keefo/optic/worklogs/2026-09-21-focus-tools.md

# Dated Worklog: 2026-09-21 - Focus Tools: Histogram, Focus Peaking, Loupe

Status: **user-accepted** (2026-09-21): implemented, tested, deployed to the
Pi via `--assets`, and accepted by the user in the browser. Orca worktree
`focus-tools` (branch `focus-tools`, base `main` `0f06366`).

## Objective

Setup-visit tools on the dashboard's live preview, for the manual-focus
6 mm lens: a live **histogram** with clipping readouts, **focus peaking**
(edge highlight overlay), and a **loupe** (magnified crop around a chosen
point) with a numeric **sharpness score** you can maximise by turning the
focus ring. Picked by the user from the 2026-09-21 pro-features brainstorm.

## Design

**Everything runs in the browser, on frames the page already decodes.**
`app.js` parses the MJPEG multipart stream itself and decodes each frame
into `#preview` (`renderMjpegFrame`, after `await preview.decode()`). The
frame is a same-origin blob URL, so drawing it to a canvas does not taint
the canvas. So:

- There are no Rust, camera, or API changes and no daemon restart. The tools
  ship through the `--assets` deploy path.
- The processing cost lands on the viewing computer, not the Pi.
- It works in every browser. The page never relies on `<img>` rendering
  MJPEG natively.

The components:

- **New `src/web/focus-tools.js`.** It has two halves:
  - Pure functions that take `{data, width, height}` pixel data:
    - `computeHistogram` returns R/G/B/luma bins (Rec. 709 luma) and the
      shadow and highlight clipping fractions.
    - `toGray` and `sobelMagnitude`.
    - `peakingThreshold` returns the magnitude at a sensitivity
      percentile.
    - `sharpnessScore` returns the mean squared Sobel magnitude
      (Tenengrad).
    - `loupeRect` clamps the crop to the frame.
    - `clientToImagePoint` maps a click to image pixels under
      `object-fit: contain` letterboxing.

    They are exported for Node tests via `module.exports` when it exists.
  - A small UI controller on `window.OpticFocus`. `app.js` calls
    `OpticFocus.onFrame(img)` after each rendered frame, and
    `OpticFocus.clear()` when the preview is stopped or hidden.
- **Processing budget.** A frame is processed only if the previous one has
  finished; if not, the frame is skipped. The histogram and peaking run on
  a copy downscaled to at most a 960 px long edge. The loupe reads only its
  own crop (240 × 240 source pixels) from the full-resolution frame.
- **UI** (`index.html` and `styles.css`), under the preview:
  - Three toggle buttons (`aria-pressed`): Histogram, Peaking and Loupe.
  - A peaking sensitivity slider, shown only while peaking is on.
  - The **peaking overlay** is a `<canvas>` stacked on `#preview` with the
    same `object-fit: contain` and `pointer-events: none`.
  - The **histogram** is a small translucent canvas in the preview corner,
    plus shadow and highlight clipping percentages.
  - The **loupe** is a panel with the magnified crop. It shows the sharpness
    score, the best score so far (with a reset), and the source scale. That
    scale is "1:1 sensor pixels" only when the frame is 4056 px wide
    (Master Archive with downsample off); otherwise it reads "preview
    pixels". Clicking the preview moves the focus point; the default is the
    centre.
  - The toggle state is remembered per viewer in `localStorage`, wrapped
    in try/catch. The page works without it.
- `biome.json`: add `src/web/focus-tools.js`.
- CI: the web-lint job also runs `node --test tests/web`.

**Out of scope** (possible follow-ups):

- A true sensor-resolution crop at every profile, through libcamera
  `ScalerCrop` on the Pi (a Rust and camera change).
- Clipping zebras on the image.
- Waveform or RGB parade views.

## Acceptance Criteria

1. The histogram updates with the live preview, and its clipping
   percentages respond to over- and under-exposure.
2. Peaking highlights in-focus edges. The highlighted area grows as focus
   improves, and the sensitivity slider changes how much is highlighted.
3. The loupe shows a magnified crop at the clicked point, labelled with the
   right scale, and its sharpness score peaks at best focus.
4. All three tools are off by default and cost nothing when off. There is
   no visible slowdown of the preview on a typical laptop, including the
   Master Archive full-resolution 2 fps preview.
5. Stopping or freezing the preview (capture) doesn't break the tools. The
   overlays hide or keep the last frame, and they resume with the stream.
6. Existing behaviour is unchanged: capture, profile switching, downsample,
   the responsiveness measurement, and Biome and `cargo test`.

## Test Plan (before implementation)

Local (macOS):

1. `node --test tests/web` covers the pure functions:
   - Histogram: all-black gives 100% shadow clip; all-white gives 100%
     highlight clip; a 2-value image puts counts in the right bins; luma
     weights are right for pure red, green and blue.
   - Sobel and peaking: a vertical step edge gives magnitude only at the
     edge columns, and the threshold at a high percentile keeps only edge
     pixels.
   - Sharpness: a sharp step scores higher than the same step box-blurred.
   - `loupeRect` clamps at all four corners, and handles crops larger than
     the frame.
   - `clientToImagePoint` is right for letterboxing on both axes, and for a
     click outside the image.
2. `node --check` on the JS files; Biome 2.5.14 `ci` (via `npx`).
3. `cargo test` (the `web.rs` asset tests, plus a new assertion that
   `index.html` loads `focus-tools.js`).
4. CI on the PR.

On the Pi (needs user approval for an `--assets` deploy; no daemon restart):

5. The served `/focus-tools.js` matches the branch.
6. User browser acceptance of criteria 1–5, in Master Archive (full and
   downsampled) and in one small-preview profile.

## Handover (2026-09-21): work done so far, uncommitted in this worktree

Done:

- `src/web/focus-tools.js` (new): the pure functions and the browser
  controller (`window.OpticFocus.onFrame` / `.clear`), as designed above.
  Two design refinements from the draft:
  - Peaking uses an **absolute** Sobel threshold (`peakingThreshold`:
    220 → 40), not a percentile. A defocused frame must light up less.
  - The loupe scores a 160 px source crop at 1:1 and shows it at 2×,
    nearest-neighbour.
- `tests/web/focus-tools.test.js` (new): `node --test tests/web`.
  **12/12 pass** (Node 26.8.2, macOS).
- `src/web/index.html`:
  - loads `/focus-tools.js` before `/app.js`;
  - adds the peaking overlay canvas and histogram panel inside
    `.preview-frame`;
  - adds the focus-tools toolbar (3 toggles + sensitivity slider) and the
    loupe panel above the downsample option.
- `src/web/app.js`: two hooks. `window.OpticFocus?.onFrame(elements.preview)`
  runs after `recordRenderedFrame`, so the latency measurement is
  unaffected; `window.OpticFocus?.clear()` runs in `hidePreview`.
- `src/web/styles.css`: the focus-tools block is appended at the end.
- `biome.json`: `src/web/focus-tools.js` added to `files.includes`.
- `src/web.rs`: new test `focus_tools_are_wired_into_the_dashboard`. It
  checks the script order and the hooks, and that every `$("#id")` in
  focus-tools.js exists in index.html. `cargo test --locked`: **171
  passed** (macOS).
- `node --check src/web/focus-tools.js`: ok.

Remaining:

1. Biome 2.5.14 `ci` locally (not installed; try
   `npx @biomejs/biome@2.5.14 ci`), and fix anything it reports.
2. CI: add `node --test tests/web` to the `web-lint` job in
   `.github/workflows/ci.yml`. Check `scripts/ci-changed-scope.sh`: a
   `tests/web` change must not count as docs-only.
3. Write `docs/optic-daemon-focus-tools.md` (referenced from
   focus-tools.js). Add a short pointer in `docs/optic-daemon.md` (the
   dashboard section) and the README Camera Daemon paragraph.
4. With user approval: `./scripts/build-deploy-optic-daemon.sh --assets`
   (no daemon restart). Check that the served `/focus-tools.js` matches
   the branch. Then the user does the browser acceptance of criteria 1–5
   in Master Archive (full and downsampled) and one small-preview profile.
5. Close this worklog, then commit, push the branch and open a PR (with
   user approval).

## Progress (2026-09-21, Orca agent session): Remaining items 1–3

1. **Biome 2.5.14 `ci`** (`npx @biomejs/biome@2.5.14 ci`). The first run
   found 2 errors and 1 warning, all fixed:
   - warning `lint/suspicious/noRedundantUseStrict` in `focus-tools.js`:
     removed `"use strict";` (no other dashboard script uses it; the file is
     a classic script and does not depend on strict mode);
   - `format` in `focus-tools.js` (`clear()`): applied `biome format --write`;
   - `lint/a11y/useSemanticElements` on `<div role="group">` in
     `index.html`: it is now a `<fieldset class="focus-tools"
     aria-label="Focus tools">`. `.focus-tools` in `styles.css` now sets
     `flex-direction: row`, `min-width: 0` and `margin`, so the global
     `fieldset` rules (including the narrow-screen `flex-direction:
     column`) do not stack the toggles.

   Re-run: `Checked 11 files ... No fixes applied.`, exit 0.
2. **CI:** `web-lint` in `.github/workflows/ci.yml` now also runs
   `node --version && node --test tests/web` on the runner's preinstalled
   Node. No new action or npm dependency; the tests use `node:test` only.
   `scripts/ci-changed-scope.sh` needed no change, since only `*.md`,
   `docs/*`, `worklogs/*` and `case/*` count as docs. Checked:
   `printf 'tests/web/focus-tools.test.js\nworklogs/x.md\n' |
   scripts/ci-changed-scope.sh` gives `docs_only=false`. Documented in
   `docs/optic-daemon-ci-cd.md` §4 and §5.1.
3. **Docs:** new `docs/optic-daemon-focus-tools.md`. Pointers added in
   `docs/optic-daemon.md` (Web Service, Responsibilities) and in the README
   Camera Daemon paragraph.

Local re-verification after these changes (macOS, Node 26.8.2):

- `node --check src/web/focus-tools.js`: ok. `node --test tests/web`:
  12/12 pass.
- `npx @biomejs/biome@2.5.14 ci`: clean.
- `cargo fmt --check`: it flagged the new `src/web.rs` test (one long
  `assert!`). Fixed with `cargo fmt`, which changed only `src/web.rs`.
- `cargo test --locked`: 171 passed, including
  `focus_tools_are_wired_into_the_dashboard`.
- `cargo clippy --locked --all-targets -- -D warnings`: clean.

Pre-deploy check of the Pi (read-only):

- `optic-daemon.service` is active.
- `/focus-tools.js` returns 500 (the missing-asset response).
- Every tracked `src/web` file the Pi serves matches `HEAD` (`0f06366`),
  and `origin/main` has not moved. So an `--assets` deploy from this
  worktree changes only `app.js`, `index.html` and `styles.css`, and adds
  `focus-tools.js`. It does not overwrite another track's files.

Doc mismatch noticed, not fixed here (outside this track): the README Camera
Daemon paragraph still says the daemon runs as "`liam`'s persistent systemd
user service", but since PR #12 it is a system service.

## Deploy (2026-09-21, user-approved): item 4

- `./scripts/build-deploy-optic-daemon.sh --assets`: the Pi-side Biome run
  checked 11 files with no fixes, it installed with rollback protection, and
  it ended with
  `SUCCESS: static web assets deployed and verified at http://optic.local:8000/`.
  The only ERROR in the service log (05:11:29 UTC,
  `failed to load web asset ... focus-tools.js`) was the pre-deploy
  read-only probe, from before the file existed.
- Served content vs the worktree (SHA-256 over HTTP): `focus-tools.js`,
  `app.js`, `index.html`, `styles.css`, `footer.js` and `scheduler.js` all
  **match**. `/focus-tools.js` returns 200 `text/javascript; charset=utf-8`.
- No restart: `optic-daemon.service` is active, with `ActiveEnterTimestamp`
  unchanged at 21:44:05 PDT (before the deploy).

Status: **deployed**. The browser acceptance of criteria 1–5 is pending
with the user.

## Change from user acceptance (2026-09-21): drag to move the loupe

User feedback during acceptance: clicking moves the loupe, but "I
naturally click down and drag, hope it would follow my drag, but it does
not." I reproduced this in Chrome: a click moved the box from the centre to
the top-left, and a drag did nothing beyond the initial press.

Plan:

- Replace the `click` handler on `#preview` with pointer events. While the
  loupe is on:
  - `pointerdown` (primary button) places the point and captures the
    pointer;
  - `pointermove` while captured follows the pointer, clamped to the image
    edges so dragging past the letterbox pins the box to the edge;
  - `pointerup` or `pointercancel` ends the drag.
- Redraws during a drag are coalesced to one per animation frame. Moving
  the point resets "best", as a click already did.
- Suppress the browser's native image drag (`dragstart`) and set
  `touch-action: none` while the loupe is on, so touch drags work.
- `clientToImagePoint` gains an optional `clamp` argument. The default
  (null outside the image) is unchanged for the initial press.

Tests first: in `node --test tests/web`, `clientToImagePoint` with
`clamp=true` pins points in the letterbox and outside the element to the
image edges, and leaves inside points unchanged. The existing tests must
still pass.

Acceptance: press on the preview and drag. The green box and the loupe
crop follow the pointer smoothly (Master Archive full, downsampled, and a
small profile). Dragging past the image edge pins the box to the edge, and
a plain click still works.

Implementation (drag):

- **`focus-tools.js`:**
  - `clientToImagePoint(..., clamp = false)`;
  - the `click` handler replaced by `pointerdown`, `pointermove`,
    `pointerup` and `pointercancel` with pointer capture;
  - rAF-coalesced redraws (`moveLoupeTo`);
  - `dragstart` suppressed while the loupe is on.
- **`styles.css`:** `img.loupe-target` gets `touch-action: none;
  user-select: none`.
- **`index.html`:** the hint now reads "Click or drag on the preview to move
  the loupe."
- **`docs/optic-daemon-focus-tools.md`:** §2 table and §3.4, §3.5 updated.

Verification:

- The new test failed first (12 pass, 1 fail) and passes after the change:
  `node --test tests/web` gives 13/13.
- `npx @biomejs/biome@2.5.14 ci`: clean. `cargo test --locked`: 171
  passed.
- The user approved a second `--assets` deploy:
  - Pi Biome clean; the script ended with `SUCCESS: static web assets
    deployed and verified`.
  - Served `focus-tools.js`, `index.html`, `styles.css` and `app.js` match
    the worktree (SHA-256).
  - `ActiveEnterTimestamp` unchanged at 21:44:05 PDT, so no restart.
- Agent browser check (Chrome, Master Archive, downsampled 1352 × 1014
  preview):
  - dragging from the centre moved the box and the crop to the top-left;
  - dragging far past the bottom-right corner pinned the box at that
    corner;
  - there were no console errors.
  - This is an agent check, not user acceptance.

## Close (2026-09-21)

**User acceptance:** after the drag change, the user checked the dashboard
and replied "looks good commit create pr". Criteria 1–5 are accepted.
Criterion 6 is covered by `cargo test` (171), Biome `ci` and the unchanged
latency hook order.

**Files changed:**

- New:
  - `src/web/focus-tools.js`
  - `tests/web/focus-tools.test.js`
  - `docs/optic-daemon-focus-tools.md`
  - this worklog
- Modified:
  - `src/web/app.js` (2 hooks)
  - `src/web/index.html`
  - `src/web/styles.css` (focus-tools block at the end)
  - `src/web.rs` (test `focus_tools_are_wired_into_the_dashboard`)
  - `biome.json`
  - `.github/workflows/ci.yml` (`node --test tests/web` in `web-lint`)
  - `docs/optic-daemon-ci-cd.md`
  - `docs/optic-daemon.md`
  - `README.md`
- Not changed: `Cargo.toml` (version stays 0.1.31), Rust runtime code,
  camera, API and systemd.

**Final results:**

- `node --test tests/web`: 13/13.
- `npx @biomejs/biome@2.5.14 ci`: clean.
- `cargo fmt --check`: clean. `cargo clippy --locked --all-targets -D
  warnings`: clean. `cargo test --locked`: 171 passed.
- Deployed assets match the branch, with no daemon restart.
- GitHub CI runs on the PR, including the new Node step.

**Limitations and follow-ups:**

- The loupe is 1:1 with the sensor only in Master Archive with downsampling
  off. A sensor-resolution crop in every profile would need libcamera
  `ScalerCrop` (Rust and camera).
- No zebras, waveform or RGB parade.
- The histogram comes from the JPEG preview, not RAW.
- The new CI step relies on the runner's preinstalled Node. If a future
  image drops Node, add a SHA-pinned `actions/setup-node`.
- README mismatch, outside this track: it still says "systemd user
  service" (it has been a system service since PR #12).

## CI fix (2026-09-21, after PR #13 opened)

PR #13 CI: `Biome (web assets)` failed on both the push and pull_request
runs. `biome ci` passed; the new step failed. The runner has Node
**v22.23.2**, which treats `node --test tests/web` as a module path:
`Error: Cannot find module '/home/runner/work/optic/optic/tests/web'`,
with 0 tests run. Local Node 26 discovers test files in a directory, which
is why it passed locally. The other checks passed: Rust (Debian 13
arm64), Timelapse tool (macOS) and Detect changed scope.

Fix: CI now runs `node --test tests/web/*.test.js` (bash expands the glob;
this works on every Node that has `node:test`). The same form is now used
in the test-file header comment, `docs/optic-daemon-ci-cd.md` (§4 and
§5.1) and `docs/optic-daemon-focus-tools.md`. The lesson is recorded in
`AGENTS.md`, under Environment and Tooling Constraints.

Local check: `node --test tests/web/*.test.js` gives 13/13.
