keefo/optic/worklogs/2026-09-20-ci-phase1-gates.md

# Dated Worklog: 2026-09-20 - CI Phase 1: GitHub Actions Gates

Status: **implemented and tested on GitHub Actions**. All acceptance
criteria (AC1–AC6) passed.

- Nothing was deployed. The Pi was not touched.
- The CI-built binary has **not** been hardware-validated; that is phase 2.
- Awaiting user acceptance.

Plan: [`docs/optic-daemon-ci-cd.md`](../docs/optic-daemon-ci-cd.md) §7 phase 1.
Research: [`2026-09-20-github-ci-cd-plan.md`](2026-09-20-github-ci-cd-plan.md).
User decisions (2026-09-20): implement phase 1; D2 = add `rust-toolchain.toml`.

## Objective

Run the deploy script's gates on every push and PR, on GitHub-hosted runners:

- fmt;
- test;
- strict Clippy;
- Biome;
- the release build, with `ldd` and version checks.

The release binary is kept as a downloadable CI artifact. There is no
release or deploy step in this phase.

## Scope

1. `rust-toolchain.toml` (`channel = "1.98.1"`, with rustfmt and Clippy).
   The deploy script reads `RUST_VERSION` from it instead of hard-coding it.
2. The Biome file list moves into `biome.json` `files.includes`. The deploy
   script and CI both run Biome without explicit paths.
3. `scripts/ci-install-build-deps.sh` installs the native packages in a
   `debian:trixie` container:
   - it adds the Raspberry Pi archive with the key fingerprint pinned to
     `CF8A1AF502A2AA2D763BAE7E82B129927FA3303E`;
   - it installs the exact `required_packages` list parsed from
     `scripts/build-deploy-optic-daemon.sh`, so the pins exist in one place.
4. `.github/workflows/ci.yml` with two jobs, `web-lint` and `rust-arm64`.
5. `.github/dependabot.yml` for `github-actions` only.

Out of scope: `release.yml`, the `--release` deploy mode, any Pi changes,
and branch protection (D1).

## Acceptance Criteria

- AC1: `actionlint` reports no errors on `ci.yml`, and `bash -n` passes on
  the changed scripts.
- AC2: Biome 2.5.14 with the new `files.includes` checks exactly the nine
  files the script checked before (`app.js`, `index.html`, `scheduler.js`,
  `scheduler.html`, `capture-history.js`, `capture-history.html`,
  `config.js`, `config.html`, `footer.js`). It passes on the current tree
  and fails on a deliberately mis-formatted file.
- AC3: The `required_packages` parse yields the same nine pins the script
  uses.
- AC4: Parsing `rust-toolchain.toml` yields `1.98.1`. Local cargo still
  passes fmt, test and Clippy.
- AC5: **(requires a push, gated on user approval)**
  - A GitHub Actions run on this branch is green in both jobs.
  - The Linux test count is recorded.
  - The `ldd` and version checks pass and the artifact is downloadable.
  - Cold and warm durations are recorded.
- AC6 (negative, requires a push): a deliberate fmt violation turns the run
  red. Run it once, then revert.

## Failure Cases to Watch

- The RPi repo may pull in newer packages than the pins, causing an apt
  resolution conflict. The script fails loudly; it does not float versions.
- Clippy may fail with LLVM 19 vs 22 in the container. If so, port the
  deploy script's wrapper and record that.
- bindgen may be unable to find headers or libclang. `LIBCLANG_PATH` and
  `BINDGEN_EXTRA_CLANG_ARGS` mirror the Pi script.
- Tests may assume a host-specific environment such as tmpfs or `/proc`.

## Target Environments

- Local macOS: static checks, Biome, and cargo on the non-Linux code path.
- GitHub-hosted `ubuntu-24.04-arm` with a `debian:trixie` container: the
  real CI (AC5 and AC6).
- The Pi is **not** touched. Deploy-script edits are checked with `bash -n`
  and local extraction tests only. A real deploy is needed to hardware-verify
  them.

## Implementation Summary

Files changed:

- `rust-toolchain.toml` (new): `channel = "1.98.1"`, with the rustfmt and
  Clippy components and the minimal profile.
- `biome.json`:
  - adds `files.includes` with the nine web files;
  - adds a trailing newline. The file had none before, and Biome now checks
    its own config once no paths are passed, so the missing newline was a
    new failure.
- `scripts/build-deploy-optic-daemon.sh`:
  - uploads `rust-toolchain.toml` and requires it to be present;
  - on the Pi, reads `RUST_VERSION` from it and validates the format;
  - runs `"$HOME/biome" check` with no paths;
  - adds a comment documenting that CI parses `required_packages`.
- `scripts/ci-install-build-deps.sh` (new): the root-only installer for the
  arm64 trixie container. It:
  - takes the Raspberry Pi archive key from the
    `raspberrypi-archive-keyring_2025.1+rpt1_all.deb` package, pinned by
    SHA-256, then checks the key fingerprint;
  - writes a deb822 source with `Signed-By`;
  - installs the parsed pins with `--print-packages` available for dry runs;
  - uses a read loop instead of `mapfile`, because macOS bash 3.2 has no
    `mapfile`.
- `.github/workflows/ci.yml` (new) has two jobs, `web-lint` and
  `rust-arm64`:
  - every action is pinned to a commit SHA: checkout v7.0.1
    `3d3c42e5…`, setup-biome v2.7.1 `4c91541e…`, rust-cache v2.9.2
    `6323deb1…`, upload-artifact v7.0.1 `043fb46d…`;
  - SHAs were resolved with `git ls-remote`, using the peeled `^{}` commit
    for annotated tags.
- `.github/dependabot.yml` (new): weekly grouped `github-actions` updates
  only.
- Docs: `docs/optic-daemon-ci-cd.md` (status, §2, §5.1, D2 resolved) and
  `docs/optic-daemon-build-environment.md` (the new single sources).

Design deviation from the plan: CI installs the **same** nine
`required_packages` pins as the Pi, with
`LIBCLANG_PATH=/usr/lib/aarch64-linux-gnu`, instead of the separately
listed `libclang-19-dev`. This keeps the Pi and CI on one pin list. The plan
doc was updated to match.

## Validation

Environment: the macOS development host. No Linux or arm64 container was
available locally: no Docker, and the `vmpi-builder` Lima VM is x86_64
without qemu-user.

| AC | Command | Observed |
| --- | --- | --- |
| AC1 | `actionlint` 1.7.12 with shellcheck 0.11.0 on `PATH` | First run: 2× SC2094 (info). The checksum step read and wrote `SHA256SUMS` in the same pipeline; fixed by writing to a temp file outside the hashed directory and then `mv`. Rerun: exit 0 |
| AC1 | `shellcheck scripts/ci-install-build-deps.sh` | SC1091 (info) on `. /etc/os-release`; added a `source=/dev/null` directive. Rerun: exit 0 |
| AC1 | `bash -n` on both scripts | OK. The deploy script's shellcheck finding count is unchanged vs `HEAD` (1 existing) |
| AC2 | Biome 2.5.14 (`npx @biomejs/biome@2.5.14`) `check --verbose` | The processed set is exactly the nine listed files, plus `biome.json` |
| AC2 | Baseline: `HEAD` `biome.json` with the old explicit nine paths | `Checked 9 files … No fixes applied` |
| AC2 | New `biome check` / `biome ci` before the newline fix | 1 error: `biome.json` format (missing trailing newline) |
| AC2 | New `biome check` / `biome ci` after the fix | `Checked 10 files`, exit 0 |
| AC2 | Negative test: a copy with a mis-formatted line appended to `footer.js` | `biome ci` exit 1, `biome check` exit 1 |
| AC3 | `scripts/ci-install-build-deps.sh --print-packages` | The nine pins, identical to `required_packages`. `--bogus` gives exit 1; running as non-root gives exit 1 "must run as root" |
| AC3 | Each pin is present in the Debian trixie and RPi trixie arm64 `Packages` indexes | 9/9 OK |
| AC4 | `sed` parse of `rust-toolchain.toml` | `1.98.1` |
| AC4 | Local `cargo fmt --check`, `cargo test --locked --all-targets`, `cargo clippy … -D warnings` (Homebrew cargo 1.98.1, which ignores `rust-toolchain.toml`) | fmt OK; `109 passed; 0 failed`; Clippy clean |
| AC5 | Run `35567448224` (commit `e04a755`) | **Failed** at "Install pinned native build dependencies". See Failures Encountered |
| AC5 | Run `35567649875` (commit `b09f7c4`, cold cache) | **Success.** Biome 5s; the Rust job took 4m35s in total |
| AC6 | Run `35568071487` (commit `64dabda`, a deliberate extra space in `src/main.rs` `fn main`) | **Failure** at the `cargo fmt` step (`Diff in …/src/main.rs:32`). Biome still passed. Reverted in `acc0002` |
| AC5 | Run `35568193008` (commit `acc0002`, warm cache) | **Success.** The Rust job took 1m45s in total |

AC5 details from run `35567649875`:

- Step times on a cold cache:
  - dependency install: 20s;
  - toolchain: 6s;
  - `cargo test`: 64s;
  - Clippy: 28s;
  - release build (LTO, `codegen-units = 1`): 100s;
  - cache save: 41s.
- Step times on a warm cache (run `35568193008`):
  - dependency install: 20s;
  - cache restore: 11s;
  - test: 9s;
  - Clippy: 3s;
  - release build: 39s.
- Linux tests: `112 passed; 0 failed` in the main target, plus
  `4 passed; 0 failed` in `libcamera_probe`. That is 116 in total, vs 109
  on macOS; the difference is the `cfg(target_os = "linux")` tests.
- Clippy `-D warnings` passed **without** the Pi's LLVM-isolating
  compiler wrapper, as expected, because the container installs libclang
  system-wide.
- `ldd` resolved every library with no `not found`. The binary links
  `/lib/aarch64-linux-gnu/libcamera.so.0.7`, `libcamera-base.so.0.7` and
  `libturbojpeg.so.0`. The embedded-version check for `0.1.29` passed.
- The artifact `optic-daemon-0.1.29-aarch64-linux-gnu-b09f7c437246` is
  about 2.0 MB and expires 2026-10-05. It was downloaded with
  `gh run download`, and `shasum -a 256 -c SHA256SUMS` reported 15/15 OK.
  `file` reports `ELF 64-bit LSB pie executable, ARM aarch64 … stripped`;
  it is 5,331,752 bytes, and the executable bit survived the round trip.
  `VERSION` is `0.1.29` and `COMMIT` is `b09f7c43…`.

The RPi archive key fingerprint was computed from
`raspberrypi.gpg.key` (sha256 `76603890…6d56`) with a Python OpenPGP v4
fingerprint calculation, because no `gpg` was available on the Mac or the
VM. Primary key: `CF8A1AF502A2AA2D763BAE7E82B129927FA3303E`, uid
"Raspberry Pi Archive Signing Key".

## Failures Encountered

- `mapfile: command not found` under the macOS bash 3.2. Replaced with a
  `while read` loop. `CLAUDE.md` asks for such findings to be recorded in
  `AGENTS.md`, but that file does not exist in this checkout (plan O4), so
  the finding is recorded here instead.
- Biome's config-file check exposed the missing trailing newline in
  `biome.json`. Fixed as described above.
- **First CI run failed:** apt refused the Raspberry Pi archive.
  - The error from `sqv` was `Signing key on CF8A1AF5…7FA3303E is not
    bound … SHA1 is not considered secure since 2026-02-01`. The key served
    at `raspberrypi.gpg.key` carries SHA-1 self-signatures (checked locally:
    the uid and subkey bindings are both SHA-1).
  - The `raspberrypi-archive-keyring 2025.1+rpt1` package ships the **same**
    key, with SHA-512 bindings, as `usr/share/keyrings/raspberrypi-archive-keyring.pgp`.
    The package's SHA-256 (`2e727149…60e4`) matched the RPi `Packages`
    index.
  - Fix (commit `b09f7c4`): download that `.deb`, check its pinned SHA-256
    and the key fingerprint, and use the `.pgp` as `Signed-By`.
  - The pinned fingerprint check itself had passed, which confirms it was
    matching the correct key.
- Command mistake: `git revert -q` does not exist (`git revert` has no
  quiet flag). Used `git revert --no-edit HEAD >/dev/null` instead. As
  with `mapfile`, this is recorded here because there is no `AGENTS.md`.

## Limitations and Next Steps

- Pinning `raspberrypi-archive-keyring` means CI fails loudly if the RPi
  archive rotates its key or withdraws that package version. That is the
  intended behaviour; update the pin deliberately.
- The branch history includes the AC6 negative-test commit and its revert
  (`64dabda`, `acc0002`), by design.
- The deploy-script edits (reading `RUST_VERSION` from the file, Biome with
  no paths) have **not** run on the Pi. The next real `build-deploy` run,
  full or `--assets`, will exercise them. Plan item O1: check that the Pi's
  `~/biome` is a 2.x version that supports `files.includes`.
- Nothing was deployed; phase 2 (a hardware test of the CI artifact) needs
  explicit approval.
