keefo/optic/worklogs/2026-09-20-scheduler-phase2e-capture-log-source-fix-and-doc-resolution.md

# Dated Worklog: 2026-09-20 - Scheduler Phase 2e: Capture-Log Source Fix, `triggered_by`, and Design-Doc Resolution

Status: **implemented, deployed, and verified.**

## Objective

Two small, explicitly-deferred follow-ups from the earlier
`2026-09-20-scheduler-capture-filename-tagging.md` worklog, plus closing
out the design doc's now-almost-entirely-resolved §14 open-decisions
list:

1. `optic_capture_log.rs::failure_capture_id` always said `testshot-`
   for a *failed* scheduler capture's synthetic log-only id, regardless
   of actual source.
2. `CaptureLogEntry.source` was a plain string with no structured record
   of which rule(s) triggered a scheduler capture.
3. `docs/optic-daemon-scheduler.md`'s top-of-file status and §14 still
   read as an in-progress design proposal despite Phase 1 and (as of
   tonight) most of Phase 2 being fully implemented and deployed.

## Implementation Summary

### `src/optic_capture_log.rs`

- Root cause of item 1: `CaptureLogEntry::new()` always hardcoded
  `source: "web_ui".to_owned()` internally and computed `capture_id`
  (via `derive_capture_id`/`failure_capture_id`) *before* the one caller
  that needed something different (`optic_scheduler.rs`'s `fire_capture`)
  patched `entry.source` afterward — too late for the id itself to ever
  reflect it.
- Fixed by threading the real `CaptureSource` (already known at both
  call sites — `web.rs`'s `capture()` has it on the incoming
  `CaptureRequest`, `optic_scheduler.rs`'s `fire_capture` constructs it
  directly) into `CaptureLogEntry::new()` as a new parameter, used by
  both `derive_capture_id`/`failure_capture_id` (for the id prefix) and
  to set `source`/the new `triggered_by` field correctly from the start
  — no more post-hoc patching.
- `CaptureLogEntry` gained `#[serde(default)] triggered_by: Vec<String>`
  — empty for `WebUi`, the firing rule slugs for `Scheduler`. No
  database schema migration needed: the whole entry is persisted
  verbatim as the `detail_json` column (per this module's own doc
  comment), so a new struct field just flows into that JSON blob.
  `#[serde(default)]` specifically so a `.log.json` file or database row
  written before this field existed still deserializes (as empty)
  rather than failing — matters because these files/rows are genuinely
  durable and outlive any given daemon version.
- `web.rs`/`optic_scheduler.rs` call sites: both now extract
  `request.source.clone()` *before* `request` is moved into
  `capture_to_stage`, and pass it through — `optic_scheduler.rs` no
  longer needs the post-hoc `entry.source = "scheduler".to_owned()`
  line at all, removed.

### `docs/optic-daemon-scheduler.md`

- Top-of-file `> Status:` line: "design proposal, not implemented" →
  reflects Phase 1 (shipped 2026-09-19) and Phase 2 (shipped
  2026-09-20), pointing at the dated worklogs for the actual record.
- §2's `Constraints` data-model prose: "`time_window` is the only field
  implemented today... the rest are Phase 2+" → all five fields are now
  implemented, dated accordingly.
- §14: added six new **Resolved** entries (merge-window duration bumped
  to 10s with the measured-data rationale; Station config as a plain
  manual dashboard form; the `astro` crate decision and why it
  eliminated the previously-separate lunar-crate research item;
  `Trigger::Ephemeris` fully implemented and live-verified; the Storage
  Forecaster; the dead-rule/overlap advisories) and updated the
  `testshot-`-prefix entry's "Not done" list to "now also done" for both
  previously-deferred items — turning §14 from a genuine open-questions
  list into what it now actually is, a resolved-decisions log with
  pointers to the worklog that implemented and verified each one.
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
