keefo/optic/src/optic_capture_log.rs

//! Passive observer of every capture request `optic_web` (and, later,
//! `optic_scheduler`) issues to `optic_camera`: durably records what was
//! requested, whether it succeeded, and basic output metadata, so capture
//! history survives past a single `tracing` session. See
//! `docs/optic-daemon-capture-log.md` for the full design and
//! `worklogs/2026-09-18-capture-history-module.md` for the decisions behind
//! this scope.
//!
//! Two best-effort writes per capture — neither can affect whether the
//! capture itself succeeded, and a failure in either is logged and
//! swallowed rather than surfaced to the HTTP caller:
//! - a `<capture_id>.log.json` file dropped into the capture directory,
//!   picked up and transferred by `optic_sync` exactly like the JPEG/DNG
//!   files it's paired with;
//! - a row in a local SQLite database, for fast Pi-side dashboard queries
//!   that per-file scanning can't answer efficiently (date-range counts,
//!   duration trends).

use std::{
    path::{Path, PathBuf},
    sync::{
        Arc, Mutex,
        atomic::{AtomicU64, Ordering},
    },
    time::{SystemTime, UNIX_EPOCH},
};

use rusqlite::{Connection, OptionalExtension};
use serde::{Deserialize, Serialize};
use tracing::warn;

use crate::camera::{
    CameraError, CameraSettings, CaptureFile, CaptureProfile, CaptureResult, CaptureSource,
};

static LAST_FAILURE_SUFFIX: AtomicU64 = AtomicU64::new(0);

/// One capture's worth of what was requested and what happened, persisted
/// verbatim as both the `.log.json` file body and the SQLite row's
/// `detail_json` column.
#[derive(Debug, Serialize, Deserialize)]
pub struct CaptureLogEntry {
    pub capture_id: String,
    pub source: String,
    /// The rule slug(s) that triggered this capture — empty for
    /// `CaptureSource::WebUi`, populated for `CaptureSource::Scheduler`.
    /// Structured alongside `source`'s plain string, per the design doc's
    /// own follow-up note (`docs/optic-daemon-scheduler.md` §3.1): lets
    /// the dashboard show/filter "what triggered this shot" without
    /// re-parsing filenames. `#[serde(default)]` so a `.log.json` file or
    /// database row written before this field existed still deserializes
    /// (as empty) rather than failing.
    #[serde(default)]
    pub triggered_by: Vec<String>,
    pub requested_at_unix_ms: u128,
    pub completed_at_unix_ms: u128,
    pub duration_ms: u128,
    pub profile: CaptureProfile,
    pub settings: CameraSettings,
    pub save_dng: bool,
    pub success: bool,
    pub error: Option<String>,
    pub files: Vec<CaptureFile>,
    pub bytes: u64,
    pub width: Option<u32>,
    pub height: Option<u32>,
    /// What the camera *actually* did: the output frame's own metadata
    /// (shutter, analogue gain, colour gains) and its brightness meter, as
    /// opposed to `settings`, which is what was **requested**. `None` for a
    /// failed capture or a backend that reports no metadata.
    /// `#[serde(default)]` so sidecars and rows written before this field
    /// existed still parse (`worklogs/2026-09-22-capture-exposure-metadata.md`).
    #[serde(default)]
    pub exposure: Option<crate::camera::CaptureExposure>,
}

impl CaptureLogEntry {
    /// Builds an entry from the same request fields and
    /// `Result<CaptureResult, CameraError>` the HTTP handler already has,
    /// without consuming it — `web.rs::capture()` still needs `outcome` to
    /// build its own response afterward.
    #[allow(clippy::too_many_arguments)]
    pub fn new(
        requested_at: SystemTime,
        completed_at: SystemTime,
        duration_ms: u128,
        profile: CaptureProfile,
        settings: CameraSettings,
        save_dng: bool,
        source: &CaptureSource,
        outcome: &Result<CaptureResult, CameraError>,
    ) -> Self {
        let capture_id = derive_capture_id(profile, source, outcome);
        let (source_str, triggered_by) = match source {
            CaptureSource::WebUi => ("web_ui".to_owned(), Vec::new()),
            CaptureSource::Scheduler { rule_slugs } => ("scheduler".to_owned(), rule_slugs.clone()),
        };
        let (success, error, files, bytes, width, height) = match outcome {
            Ok(result) => (
                true,
                None,
                result
                    .files
                    .iter()
                    .map(|file| CaptureFile {
                        filename: file.filename.clone(),
                        bytes: file.bytes,
                    })
                    .collect(),
                result.bytes,
                Some(result.width),
                Some(result.height),
            ),
            Err(error) => (false, Some(error.to_string()), Vec::new(), 0, None, None),
        };
        Self {
            capture_id,
            source: source_str,
            triggered_by,
            requested_at_unix_ms: unix_ms(requested_at),
            completed_at_unix_ms: unix_ms(completed_at),
            duration_ms,
            profile,
            settings,
            save_dng,
            success,
            error,
            files,
            bytes,
            width,
            height,
            exposure: outcome.as_ref().ok().and_then(|result| result.exposure),
        }
    }
}

fn unix_ms(time: SystemTime) -> u128 {
    time.duration_since(UNIX_EPOCH)
        .unwrap_or_default()
        .as_millis()
}

/// On success, shares the JPEG's own basename (matching design doc §3.1's
/// shared-basename convention) without needing to thread an ID down through
/// the actor into `native_camera.rs`. On failure there's no output file to
/// borrow a basename from, so a synthetic id is minted instead — a case the
/// original design doc example didn't illustrate; see the worklog's
/// "Decisions Made" §3 for why this is scoped this way.
fn derive_capture_id(
    profile: CaptureProfile,
    source: &CaptureSource,
    outcome: &Result<CaptureResult, CameraError>,
) -> String {
    match outcome {
        Ok(result) => result
            .files
            .first()
            .and_then(|file| file.filename.rsplit_once('.'))
            .map(|(basename, _extension)| basename.to_owned())
            .unwrap_or_else(|| failure_capture_id(profile, source)),
        Err(_) => failure_capture_id(profile, source),
    }
}

/// Matches `native_camera.rs::publish_capture`'s real-file prefix choice
/// (`scheduler-` vs `testshot-`) for the source — previously always
/// `testshot-` regardless of source, since no real file exists on a
/// failed capture to actually reach `optic_sync`'s allowlist either way;
/// fixed anyway (design doc §14's noted follow-up) since a scheduler
/// failure's synthetic log-only id reading as a manual "test shot" was a
/// real, if cosmetic, inconsistency.
fn failure_capture_id(profile: CaptureProfile, source: &CaptureSource) -> String {
    let prefix = match source {
        CaptureSource::WebUi => "testshot",
        CaptureSource::Scheduler { .. } => "scheduler",
    };
    let now = unix_ms(SystemTime::now()) as u64;
    let mut previous = LAST_FAILURE_SUFFIX.load(Ordering::Relaxed);
    let suffix = loop {
        let next = now.max(previous.saturating_add(1));
        match LAST_FAILURE_SUFFIX.compare_exchange_weak(
            previous,
            next,
            Ordering::Relaxed,
            Ordering::Relaxed,
        ) {
            Ok(_) => break next,
            Err(current) => previous = current,
        }
    };
    format!("{prefix}-{}-failed-{suffix}", profile_slug(profile))
}

fn profile_slug(profile: CaptureProfile) -> &'static str {
    profile.spec().slug
}

/// Matches the `profile` values already used across the dashboard/API
/// (`master_archive`/`dci_4k`/`binning_2k`), kept separate from the
/// filename slug (`master-archive`/`4k-dci`/`2k-binning`) used for
/// `capture_id`/filenames.
fn profile_key(profile: CaptureProfile) -> &'static str {
    match profile {
        CaptureProfile::MasterArchive => "master_archive",
        CaptureProfile::Dci4k => "dci_4k",
        CaptureProfile::Binning2k => "binning_2k",
    }
}

/// The single entry point for capture history recording.
#[derive(Clone)]
pub struct CaptureLog {
    inner: Arc<Inner>,
}

struct Inner {
    capture_dir: PathBuf,
    db: Mutex<Connection>,
}

impl CaptureLog {
    /// Opens (creating if needed) the SQLite history database at `db_path`
    /// and prepares its schema. `capture_dir` is where paired `.log.json`
    /// files are written, alongside the JPEG/DNG files `optic_sync` already
    /// drains from there.
    pub fn open(db_path: &Path, capture_dir: PathBuf) -> rusqlite::Result<Self> {
        if let Some(parent) = db_path.parent() {
            let _ = std::fs::create_dir_all(parent);
        }
        let db = Connection::open(db_path)?;
        // Crash-safety, not (only) a wear optimization: unattended
        // multi-month operation makes an abrupt power loss a realistic
        // event, and WAL substantially reduces the chance of a corrupted
        // database file from a write interrupted mid-transaction.
        db.pragma_update(None, "journal_mode", "WAL")?;
        db.execute_batch(
            "CREATE TABLE IF NOT EXISTS captures (
                capture_id TEXT PRIMARY KEY,
                captured_at INTEGER NOT NULL,
                source TEXT NOT NULL,
                profile TEXT NOT NULL,
                save_dng INTEGER NOT NULL,
                success INTEGER NOT NULL,
                duration_ms INTEGER NOT NULL,
                bytes_total INTEGER NOT NULL,
                error TEXT,
                detail_json TEXT NOT NULL,
                triggered_by TEXT NOT NULL DEFAULT ''
            );
            CREATE INDEX IF NOT EXISTS idx_captures_captured_at ON captures(captured_at);
            CREATE INDEX IF NOT EXISTS idx_captures_success ON captures(success);",
        )?;
        migrate_triggered_by_column(&db)?;
        Ok(Self {
            inner: Arc::new(Inner {
                capture_dir,
                db: Mutex::new(db),
            }),
        })
    }

    /// Records one completed capture. Both writes are best-effort; a
    /// failure here is logged and swallowed, never surfaced to the HTTP
    /// caller (see module docs).
    pub async fn record(&self, entry: CaptureLogEntry) {
        let json = match serde_json::to_string_pretty(&entry) {
            Ok(json) => json,
            Err(error) => {
                warn!(%error, capture_id = %entry.capture_id, "failed to serialize capture log entry");
                return;
            }
        };

        let log_path = self
            .inner
            .capture_dir
            .join(format!("{}.log.json", entry.capture_id));
        if let Err(error) = tokio::fs::write(&log_path, &json).await {
            warn!(%error, path = %log_path.display(), "failed to write capture log file");
        }

        let inner = self.inner.clone();
        let capture_id = entry.capture_id.clone();
        let captured_at = (entry.completed_at_unix_ms / 1000) as i64;
        let source = entry.source.clone();
        let profile = profile_key(entry.profile);
        let save_dng = entry.save_dng;
        let success = entry.success;
        let duration_ms = entry.duration_ms as i64;
        let bytes_total = entry.bytes as i64;
        let error_text = entry.error.clone();
        let detail_json = json;
        // Padded (`,slug-a,slug-b,`) rather than a bare join, so a
        // `LIKE '%,<slug>,%'` filter can't false-match a slug that's only a
        // substring of another rule's slug (e.g. "dawn" inside "dawn-2").
        let triggered_by_padded = format!(",{},", entry.triggered_by.join(","));

        let outcome = tokio::task::spawn_blocking(move || {
            let connection = inner.db.lock().expect("capture log db mutex poisoned");
            connection.execute(
                "INSERT OR REPLACE INTO captures
                 (capture_id, captured_at, source, profile, save_dng, success, duration_ms, bytes_total, error, detail_json, triggered_by)
                 VALUES (?1, ?2, ?3, ?4, ?5, ?6, ?7, ?8, ?9, ?10, ?11)",
                rusqlite::params![
                    capture_id,
                    captured_at,
                    source,
                    profile,
                    save_dng,
                    success,
                    duration_ms,
                    bytes_total,
                    error_text,
                    detail_json,
                    triggered_by_padded,
                ],
            )
        })
        .await;

        match outcome {
            Ok(Ok(_)) => {}
            Ok(Err(error)) => warn!(%error, "failed to record capture history row"),
            Err(error) => warn!(%error, "capture history insert task panicked"),
        }
    }

    /// Rolls up capture history over the last `window_hours` for the
    /// dashboard's system-health panel — the first consumer of this
    /// module's SQLite data (see `docs/optic-daemon-capture-log.md` §6,
    /// which explicitly deferred dashboard UI). Best-effort: any query
    /// failure yields an all-empty/zero result rather than propagating an
    /// error, matching this module's existing "never affect the caller"
    /// posture.
    pub async fn recent_health(&self, window_hours: u32) -> CaptureHealthStatus {
        let inner = self.inner.clone();
        let cutoff = unix_ms(SystemTime::now()) as i64 / 1000 - i64::from(window_hours) * 3600;

        tokio::task::spawn_blocking(move || {
            let connection = inner.db.lock().expect("capture log db mutex poisoned");
            let (total, successful, average_duration_ms) = connection
                .query_row(
                    "SELECT COUNT(*), COALESCE(SUM(success), 0), AVG(duration_ms)
                     FROM captures WHERE captured_at >= ?1",
                    rusqlite::params![cutoff],
                    |row| {
                        Ok((
                            row.get::<_, i64>(0)?,
                            row.get::<_, i64>(1)?,
                            row.get::<_, Option<f64>>(2)?,
                        ))
                    },
                )
                .unwrap_or((0, 0, None));

            let last = connection
                .query_row(
                    "SELECT captured_at, success FROM captures ORDER BY captured_at DESC LIMIT 1",
                    [],
                    |row| Ok((row.get::<_, i64>(0)?, row.get::<_, bool>(1)?)),
                )
                .optional()
                .unwrap_or(None);

            CaptureHealthStatus {
                window_hours,
                total: total.max(0) as u64,
                successful: successful.max(0) as u64,
                last_capture_at_unix_ms: last.map(|(captured_at, _)| captured_at as u128 * 1000),
                last_capture_success: last.map(|(_, success)| success),
                average_duration_ms,
            }
        })
        .await
        .unwrap_or_else(|_| CaptureHealthStatus::empty(window_hours))
    }

    /// Paginated, filtered history query for the capture-history dashboard
    /// page (`GET /api/captures`). Filters against the flat indexed columns
    /// where possible; falls back to a `LIKE` scan of the padded
    /// `triggered_by` column for the rule-slug filter, which is fine at
    /// this table's realistic size (a single Pi's lifetime capture count,
    /// not a multi-tenant workload). Each matching row's full detail is
    /// read back from `detail_json` — the same struct already used for the
    /// `.log.json` files — rather than hand-picking columns into a second,
    /// parallel response shape.
    pub async fn query(&self, filter: CaptureQueryFilter) -> CaptureQueryPage {
        let inner = self.inner.clone();
        tokio::task::spawn_blocking(move || {
            let connection = inner.db.lock().expect("capture log db mutex poisoned");

            let (where_sql, count_params) = build_where_clause(&filter);
            let count_refs: Vec<&dyn rusqlite::ToSql> =
                count_params.iter().map(|p| p.as_ref()).collect();
            let total: i64 = connection
                .query_row(
                    &format!("SELECT COUNT(*) FROM captures {where_sql}"),
                    count_refs.as_slice(),
                    |row| row.get(0),
                )
                .unwrap_or(0);

            let (_, mut select_params) = build_where_clause(&filter);
            select_params.push(Box::new(i64::from(filter.limit)));
            select_params.push(Box::new(i64::from(filter.offset)));
            let select_refs: Vec<&dyn rusqlite::ToSql> =
                select_params.iter().map(|p| p.as_ref()).collect();
            let select_sql = format!(
                "SELECT detail_json FROM captures {where_sql} ORDER BY captured_at DESC LIMIT ? OFFSET ?"
            );

            let entries = (|| -> rusqlite::Result<Vec<CaptureLogEntry>> {
                let mut statement = connection.prepare(&select_sql)?;
                let rows =
                    statement.query_map(select_refs.as_slice(), |row| row.get::<_, String>(0))?;
                let mut out = Vec::new();
                for row in rows {
                    if let Ok(entry) = serde_json::from_str::<CaptureLogEntry>(&row?) {
                        out.push(entry);
                    }
                }
                Ok(out)
            })()
            .unwrap_or_default();

            CaptureQueryPage {
                entries,
                total: total.max(0) as u64,
            }
        })
        .await
        .unwrap_or_else(|_| CaptureQueryPage {
            entries: Vec::new(),
            total: 0,
        })
    }
}

impl CaptureLog {
    /// Every capture with `since_unix <= captured_at < until_unix` (unix
    /// seconds), oldest first, as a few small columns — for the daily
    /// digest (`docs/optic-daemon-digest-heartbeat.md` §3.2), which only
    /// counts and sums, so it never parses `detail_json`. Read-only and
    /// best-effort: a query failure yields an empty list.
    pub async fn window_rows(&self, since_unix: i64, until_unix: i64) -> Vec<CaptureWindowRow> {
        const MAX_ROWS: i64 = 200_000;
        let inner = self.inner.clone();
        tokio::task::spawn_blocking(move || {
            let connection = inner.db.lock().expect("capture log db mutex poisoned");
            (|| -> rusqlite::Result<Vec<CaptureWindowRow>> {
                let mut statement = connection.prepare(
                    "SELECT captured_at, source, success, bytes_total, error FROM captures
                     WHERE captured_at >= ?1 AND captured_at < ?2
                     ORDER BY captured_at LIMIT ?3",
                )?;
                let rows = statement.query_map(
                    rusqlite::params![since_unix, until_unix, MAX_ROWS],
                    |row| {
                        Ok(CaptureWindowRow {
                            captured_at_unix: row.get(0)?,
                            source: row.get(1)?,
                            success: row.get(2)?,
                            bytes_total: row.get::<_, i64>(3)?.max(0) as u64,
                            error: row.get(4)?,
                        })
                    },
                )?;
                rows.collect()
            })()
            .unwrap_or_else(|error| {
                warn!(%error, "capture window query failed");
                Vec::new()
            })
        })
        .await
        .unwrap_or_default()
    }
}

/// One row of `CaptureLog::window_rows`.
#[derive(Debug, Clone, PartialEq)]
pub struct CaptureWindowRow {
    pub captured_at_unix: i64,
    pub source: String,
    pub success: bool,
    pub bytes_total: u64,
    pub error: Option<String>,
}

fn build_where_clause(filter: &CaptureQueryFilter) -> (String, Vec<Box<dyn rusqlite::ToSql>>) {
    let mut clauses: Vec<String> = Vec::new();
    let mut params: Vec<Box<dyn rusqlite::ToSql>> = Vec::new();

    if let Some(source) = &filter.source {
        clauses.push("source = ?".to_owned());
        params.push(Box::new(source.clone()));
    }
    if let Some(profile) = &filter.profile {
        clauses.push("profile = ?".to_owned());
        params.push(Box::new(profile.clone()));
    }
    if let Some(success) = filter.success {
        clauses.push("success = ?".to_owned());
        params.push(Box::new(success));
    }
    if let Some(rule_slug) = &filter.rule_slug {
        clauses.push("triggered_by LIKE ?".to_owned());
        params.push(Box::new(format!("%,{rule_slug},%")));
    }
    if let Some(since_unix_ms) = filter.since_unix_ms {
        clauses.push("captured_at >= ?".to_owned());
        params.push(Box::new((since_unix_ms / 1000) as i64));
    }
    if let Some(until_unix_ms) = filter.until_unix_ms {
        clauses.push("captured_at <= ?".to_owned());
        params.push(Box::new((until_unix_ms / 1000) as i64));
    }

    let where_sql = if clauses.is_empty() {
        String::new()
    } else {
        format!("WHERE {}", clauses.join(" AND "))
    };
    (where_sql, params)
}

/// Adds the `triggered_by` column to a `captures` table created before it
/// existed (any database from before tonight's Phase 2f). A no-op on a
/// fresh table, which already has the column via `CREATE TABLE`.
fn migrate_triggered_by_column(db: &Connection) -> rusqlite::Result<()> {
    let mut has_column = false;
    {
        let mut statement = db.prepare("PRAGMA table_info(captures)")?;
        let mut rows = statement.query([])?;
        while let Some(row) = rows.next()? {
            let name: String = row.get(1)?;
            if name == "triggered_by" {
                has_column = true;
                break;
            }
        }
    }
    if !has_column {
        db.execute(
            "ALTER TABLE captures ADD COLUMN triggered_by TEXT NOT NULL DEFAULT ''",
            [],
        )?;
    }
    Ok(())
}

/// Rollup of recent capture outcomes, for the system-health dashboard
/// panel. See `CaptureLog::recent_health`.
#[derive(Debug, Serialize)]
pub struct CaptureHealthStatus {
    pub window_hours: u32,
    pub total: u64,
    pub successful: u64,
    pub last_capture_at_unix_ms: Option<u128>,
    pub last_capture_success: Option<bool>,
    pub average_duration_ms: Option<f64>,
}

/// Filter + pagination parameters for `CaptureLog::query`, built by
/// `web.rs`'s `/api/captures` handler from the request's query string.
#[derive(Debug, Clone, Default)]
pub struct CaptureQueryFilter {
    pub source: Option<String>,
    pub profile: Option<String>,
    pub success: Option<bool>,
    pub rule_slug: Option<String>,
    pub since_unix_ms: Option<u64>,
    pub until_unix_ms: Option<u64>,
    pub limit: u32,
    pub offset: u32,
}

/// One page of `CaptureLog::query` results, plus the total count matching
/// the filter (independent of `limit`/`offset`) so the caller can render
/// "X-Y of Z" and enable/disable pagination controls.
#[derive(Debug, Serialize)]
pub struct CaptureQueryPage {
    pub entries: Vec<CaptureLogEntry>,
    pub total: u64,
}

impl CaptureHealthStatus {
    pub fn empty(window_hours: u32) -> Self {
        Self {
            window_hours,
            total: 0,
            successful: 0,
            last_capture_at_unix_ms: None,
            last_capture_success: None,
            average_duration_ms: None,
        }
    }
}

#[cfg(test)]
mod tests {
    use std::sync::atomic::{AtomicU64 as TestAtomicU64, Ordering as TestOrdering};

    use super::*;

    fn unique_temp_dir(label: &str) -> PathBuf {
        static COUNTER: TestAtomicU64 = TestAtomicU64::new(0);
        let id = COUNTER.fetch_add(1, TestOrdering::Relaxed);
        let dir = std::env::temp_dir().join(format!(
            "optic-capture-log-test-{label}-{}-{id}",
            std::process::id()
        ));
        std::fs::create_dir_all(&dir).expect("create temp dir");
        dir
    }

    fn exposure_sample() -> crate::camera::CaptureExposure {
        crate::camera::CaptureExposure {
            exposure_us: Some(626),
            analogue_gain: Some(1.0),
            colour_gains: Some([2.6337, 1.8228]),
            meter: Some(crate::exposure_ramp::FrameMeter {
                luminance: 0.071,
                clipped_fraction: 0.004,
                samples: 192_888,
                grey_world: Some([0.08, 0.07, 0.06]),
            }),
        }
    }

    #[test]
    fn an_entry_records_the_frames_actual_exposure_and_round_trips() {
        let mut outcome = success_outcome("testshot-master-archive-7.jpg");
        if let Ok(result) = outcome.as_mut() {
            result.exposure = Some(exposure_sample());
        }
        let entry = CaptureLogEntry::new(
            SystemTime::now(),
            SystemTime::now(),
            250,
            CaptureProfile::MasterArchive,
            CameraSettings::default(),
            false,
            &CaptureSource::WebUi,
            &outcome,
        );
        let exposure = entry.exposure.expect("actual exposure recorded");
        assert_eq!(exposure.exposure_us, Some(626));
        assert_eq!(exposure.analogue_gain, Some(1.0));
        assert_eq!(exposure.colour_gains, Some([2.6337, 1.8228]));
        assert_eq!(exposure.meter.map(|meter| meter.samples), Some(192_888));

        let json = serde_json::to_string(&entry).unwrap();
        let parsed: CaptureLogEntry = serde_json::from_str(&json).unwrap();
        assert_eq!(parsed.exposure.unwrap().exposure_us, Some(626));

        // A failed capture has no frame, so nothing to report.
        let failed: Result<CaptureResult, CameraError> = Err(CameraError::Timeout);
        let entry = CaptureLogEntry::new(
            SystemTime::now(),
            SystemTime::now(),
            250,
            CaptureProfile::MasterArchive,
            CameraSettings::default(),
            false,
            &CaptureSource::WebUi,
            &failed,
        );
        assert!(entry.exposure.is_none());
    }

    #[test]
    fn a_sidecar_written_before_this_field_existed_still_parses() {
        let legacy = r#"{"capture_id":"testshot-master-archive-1","source":"web_ui",
            "requested_at_unix_ms":1,"completed_at_unix_ms":2,"duration_ms":1,
            "profile":"master_archive","settings":{},"save_dng":false,"success":true,
            "error":null,"files":[],"bytes":0,"width":4056,"height":3040}"#;
        let parsed: CaptureLogEntry = serde_json::from_str(legacy).unwrap();
        assert!(parsed.exposure.is_none());
    }

    fn success_outcome(filename: &str) -> Result<CaptureResult, CameraError> {
        Ok(CaptureResult {
            profile: CaptureProfile::MasterArchive,
            files: vec![CaptureFile {
                filename: filename.to_owned(),
                bytes: 1234,
            }],
            bytes: 1234,
            width: 4056,
            height: 3040,
            exposure: None,
        })
    }

    #[test]
    fn capture_log_entry_round_trips_through_json() {
        let entry = CaptureLogEntry::new(
            SystemTime::now(),
            SystemTime::now(),
            250,
            CaptureProfile::Dci4k,
            CameraSettings::default(),
            false,
            &CaptureSource::WebUi,
            &success_outcome("testshot-4k-dci-1000.jpg"),
        );
        let json = serde_json::to_string(&entry).unwrap();
        let parsed: CaptureLogEntry = serde_json::from_str(&json).unwrap();
        assert_eq!(parsed.capture_id, "testshot-4k-dci-1000");
        assert!(parsed.success);
        assert_eq!(parsed.duration_ms, 250);
        assert_eq!(parsed.bytes, 1234);
        assert_eq!(parsed.source, "web_ui");
        assert!(parsed.triggered_by.is_empty());
    }

    #[test]
    fn capture_log_entry_records_the_triggering_rule_slugs_for_a_scheduler_source() {
        let source = CaptureSource::Scheduler {
            rule_slugs: vec!["dawn".to_owned(), "golden-hour".to_owned()],
        };
        let entry = CaptureLogEntry::new(
            SystemTime::now(),
            SystemTime::now(),
            250,
            CaptureProfile::MasterArchive,
            CameraSettings::default(),
            true,
            &source,
            &success_outcome("scheduler-master-archive-dawn-golden-hour-1000.jpg"),
        );
        assert_eq!(entry.source, "scheduler");
        assert_eq!(
            entry.triggered_by,
            vec!["dawn".to_owned(), "golden-hour".to_owned()]
        );
    }

    #[test]
    fn derive_capture_id_shares_the_jpeg_basename_on_success() {
        let id = derive_capture_id(
            CaptureProfile::MasterArchive,
            &CaptureSource::WebUi,
            &success_outcome("testshot-master-archive-1789753359227.jpg"),
        );
        assert_eq!(id, "testshot-master-archive-1789753359227");
    }

    #[test]
    fn derive_capture_id_mints_a_testshot_prefixed_synthetic_id_on_web_ui_failure() {
        let id = derive_capture_id(
            CaptureProfile::Binning2k,
            &CaptureSource::WebUi,
            &Err(CameraError::Timeout),
        );
        assert!(id.starts_with("testshot-2k-binning-failed-"));
    }

    #[test]
    fn derive_capture_id_mints_a_scheduler_prefixed_synthetic_id_on_scheduler_failure() {
        let source = CaptureSource::Scheduler {
            rule_slugs: vec!["dawn".to_owned()],
        };
        let id = derive_capture_id(
            CaptureProfile::Binning2k,
            &source,
            &Err(CameraError::Timeout),
        );
        assert!(
            id.starts_with("scheduler-2k-binning-failed-"),
            "expected a scheduler- prefixed id, got {id}"
        );
    }

    #[tokio::test]
    async fn record_writes_a_log_file_and_a_queryable_row_on_success() {
        let capture_dir = unique_temp_dir("success-capture-dir");
        let db_path = unique_temp_dir("success-db").join("history.db");
        let log = CaptureLog::open(&db_path, capture_dir.clone()).unwrap();

        let entry = CaptureLogEntry::new(
            SystemTime::now(),
            SystemTime::now(),
            842,
            CaptureProfile::MasterArchive,
            CameraSettings::default(),
            true,
            &CaptureSource::WebUi,
            &success_outcome("testshot-master-archive-42.jpg"),
        );
        log.record(entry).await;

        let log_file = capture_dir.join("testshot-master-archive-42.log.json");
        assert!(log_file.exists());
        let contents = std::fs::read_to_string(&log_file).unwrap();
        assert!(contents.contains("\"success\": true"));

        let connection = Connection::open(&db_path).unwrap();
        let (profile, success, duration_ms): (String, bool, i64) = connection
            .query_row(
                "SELECT profile, success, duration_ms FROM captures WHERE capture_id = ?1",
                rusqlite::params!["testshot-master-archive-42"],
                |row| Ok((row.get(0)?, row.get(1)?, row.get(2)?)),
            )
            .unwrap();
        assert_eq!(profile, "master_archive");
        assert!(success);
        assert_eq!(duration_ms, 842);

        std::fs::remove_dir_all(&capture_dir).ok();
    }

    #[tokio::test]
    async fn record_writes_a_history_row_for_a_failed_capture_with_no_output_files() {
        let capture_dir = unique_temp_dir("failure-capture-dir");
        let db_path = unique_temp_dir("failure-db").join("history.db");
        let log = CaptureLog::open(&db_path, capture_dir.clone()).unwrap();

        let entry = CaptureLogEntry::new(
            SystemTime::now(),
            SystemTime::now(),
            15,
            CaptureProfile::Dci4k,
            CameraSettings::default(),
            false,
            &CaptureSource::WebUi,
            &Err(CameraError::Busy),
        );
        let capture_id = entry.capture_id.clone();
        log.record(entry).await;

        let log_file = capture_dir.join(format!("{capture_id}.log.json"));
        assert!(log_file.exists());
        let contents = std::fs::read_to_string(&log_file).unwrap();
        assert!(contents.contains("\"success\": false"));
        assert!(contents.contains("camera is busy"));

        let connection = Connection::open(&db_path).unwrap();
        let (success, error, bytes_total): (bool, Option<String>, i64) = connection
            .query_row(
                "SELECT success, error, bytes_total FROM captures WHERE capture_id = ?1",
                rusqlite::params![capture_id],
                |row| Ok((row.get(0)?, row.get(1)?, row.get(2)?)),
            )
            .unwrap();
        assert!(!success);
        assert_eq!(error.as_deref(), Some("camera is busy"));
        assert_eq!(bytes_total, 0);

        std::fs::remove_dir_all(&capture_dir).ok();
    }

    #[test]
    fn date_range_and_average_duration_queries_work_against_the_schema() {
        let db_path = unique_temp_dir("query-db").join("history.db");
        let capture_dir = unique_temp_dir("query-capture-dir");
        let connection = CaptureLog::open(&db_path, capture_dir).unwrap();
        let connection = &connection.inner.db;
        let connection = connection.lock().unwrap();

        // Two captures on the same day, one on a different day.
        connection
            .execute(
                "INSERT INTO captures (capture_id, captured_at, source, profile, save_dng, success, duration_ms, bytes_total, error, detail_json)
                 VALUES ('a', 1758153600, 'web_ui', 'master_archive', 1, 1, 1000, 5000, NULL, '{}')",
                [],
            )
            .unwrap();
        connection
            .execute(
                "INSERT INTO captures (capture_id, captured_at, source, profile, save_dng, success, duration_ms, bytes_total, error, detail_json)
                 VALUES ('b', 1758160800, 'web_ui', 'master_archive', 1, 1, 2000, 5000, NULL, '{}')",
                [],
            )
            .unwrap();
        connection
            .execute(
                "INSERT INTO captures (capture_id, captured_at, source, profile, save_dng, success, duration_ms, bytes_total, error, detail_json)
                 VALUES ('c', 1758240000, 'web_ui', 'master_archive', 1, 1, 3000, 5000, NULL, '{}')",
                [],
            )
            .unwrap();

        let count_on_day: i64 = connection
            .query_row(
                "SELECT COUNT(*) FROM captures WHERE captured_at >= 1758153600 AND captured_at < 1758240000",
                [],
                |row| row.get(0),
            )
            .unwrap();
        assert_eq!(count_on_day, 2);

        let average_duration: f64 = connection
            .query_row("SELECT AVG(duration_ms) FROM captures", [], |row| {
                row.get(0)
            })
            .unwrap();
        assert!((average_duration - 2000.0).abs() < 0.001);
    }

    #[tokio::test]
    async fn recent_health_excludes_rows_outside_the_window_and_computes_a_rollup() {
        let db_path = unique_temp_dir("health-db").join("history.db");
        let capture_dir = unique_temp_dir("health-capture-dir");
        let log = CaptureLog::open(&db_path, capture_dir).unwrap();

        let now = (unix_ms(SystemTime::now()) / 1000) as i64;
        let within_window = now - 3600; // 1h ago
        let outside_window = now - 30 * 3600; // 30h ago, outside a 24h window

        {
            let connection = log.inner.db.lock().unwrap();
            connection.execute(
                "INSERT INTO captures (capture_id, captured_at, source, profile, save_dng, success, duration_ms, bytes_total, error, detail_json)
                 VALUES ('recent-ok', ?1, 'web_ui', 'master_archive', 1, 1, 1000, 5000, NULL, '{}')",
                rusqlite::params![within_window],
            ).unwrap();
            connection.execute(
                "INSERT INTO captures (capture_id, captured_at, source, profile, save_dng, success, duration_ms, bytes_total, error, detail_json)
                 VALUES ('recent-failed', ?1, 'web_ui', 'master_archive', 1, 0, 2000, 0, 'boom', '{}')",
                rusqlite::params![within_window + 60],
            ).unwrap();
            connection.execute(
                "INSERT INTO captures (capture_id, captured_at, source, profile, save_dng, success, duration_ms, bytes_total, error, detail_json)
                 VALUES ('too-old', ?1, 'web_ui', 'master_archive', 1, 1, 9999, 5000, NULL, '{}')",
                rusqlite::params![outside_window],
            ).unwrap();
        }

        let health = log.recent_health(24).await;
        assert_eq!(health.window_hours, 24);
        assert_eq!(health.total, 2, "the 30h-old row must be excluded");
        assert_eq!(health.successful, 1);
        assert_eq!(health.average_duration_ms, Some(1500.0));
        assert_eq!(
            health.last_capture_at_unix_ms,
            Some((within_window + 60) as u128 * 1000)
        );
        assert_eq!(health.last_capture_success, Some(false));
    }

    #[tokio::test]
    async fn recent_health_is_all_empty_when_the_database_has_no_rows() {
        let db_path = unique_temp_dir("empty-health-db").join("history.db");
        let capture_dir = unique_temp_dir("empty-health-capture-dir");
        let log = CaptureLog::open(&db_path, capture_dir).unwrap();

        let health = log.recent_health(24).await;
        assert_eq!(health.total, 0);
        assert_eq!(health.successful, 0);
        assert_eq!(health.last_capture_at_unix_ms, None);
        assert_eq!(health.average_duration_ms, None);
    }

    /// A database created before tonight's Phase 2f (`triggered_by` didn't
    /// exist yet) must open cleanly, gain the column, and let an old row
    /// read back with an empty `triggered_by` rather than failing to open
    /// or losing the row.
    #[tokio::test]
    async fn opening_a_pre_phase_2f_database_migrates_the_triggered_by_column() {
        let db_path = unique_temp_dir("legacy-db").join("history.db");
        let capture_dir = unique_temp_dir("legacy-capture-dir");
        {
            let legacy = Connection::open(&db_path).unwrap();
            legacy
                .execute_batch(
                    "CREATE TABLE captures (
                        capture_id TEXT PRIMARY KEY,
                        captured_at INTEGER NOT NULL,
                        source TEXT NOT NULL,
                        profile TEXT NOT NULL,
                        save_dng INTEGER NOT NULL,
                        success INTEGER NOT NULL,
                        duration_ms INTEGER NOT NULL,
                        bytes_total INTEGER NOT NULL,
                        error TEXT,
                        detail_json TEXT NOT NULL
                    );",
                )
                .unwrap();
            legacy
                .execute(
                    "INSERT INTO captures
                     (capture_id, captured_at, source, profile, save_dng, success, duration_ms, bytes_total, error, detail_json)
                     VALUES ('legacy-1', 1758153600, 'web_ui', 'master_archive', 1, 1, 1000, 5000, NULL, '{}')",
                    [],
                )
                .unwrap();
        }

        // Opening twice (simulating two daemon restarts) must be idempotent.
        let log = CaptureLog::open(&db_path, capture_dir.clone()).unwrap();
        drop(log);
        let log = CaptureLog::open(&db_path, capture_dir).unwrap();

        let connection = log.inner.db.lock().unwrap();
        let triggered_by: String = connection
            .query_row(
                "SELECT triggered_by FROM captures WHERE capture_id = 'legacy-1'",
                [],
                |row| row.get(0),
            )
            .unwrap();
        assert_eq!(triggered_by, "");
    }

    fn scheduler_source(rule_slugs: &[&str]) -> CaptureSource {
        CaptureSource::Scheduler {
            rule_slugs: rule_slugs.iter().map(|s| s.to_string()).collect(),
        }
    }

    async fn seed_query_fixture(log: &CaptureLog) {
        let now = SystemTime::now();
        log.record(CaptureLogEntry::new(
            now,
            now,
            100,
            CaptureProfile::MasterArchive,
            CameraSettings::default(),
            true,
            &CaptureSource::WebUi,
            &success_outcome("testshot-master-archive-1.jpg"),
        ))
        .await;
        log.record(CaptureLogEntry::new(
            now,
            now,
            200,
            CaptureProfile::Dci4k,
            CameraSettings::default(),
            false,
            &scheduler_source(&["dawn"]),
            &success_outcome("scheduler-4k-dci-dawn-2.jpg"),
        ))
        .await;
        log.record(CaptureLogEntry::new(
            now,
            now,
            300,
            CaptureProfile::Binning2k,
            CameraSettings::default(),
            false,
            &scheduler_source(&["dawn-2"]),
            &success_outcome("scheduler-2k-binning-dawn-2-3.jpg"),
        ))
        .await;
        log.record(CaptureLogEntry::new(
            now,
            now,
            400,
            CaptureProfile::MasterArchive,
            CameraSettings::default(),
            true,
            &scheduler_source(&["golden-hour"]),
            &Err(CameraError::Busy),
        ))
        .await;
    }

    #[tokio::test]
    async fn query_filters_by_source_profile_and_success_independently() {
        let db_path = unique_temp_dir("query-filter-db").join("history.db");
        let capture_dir = unique_temp_dir("query-filter-capture-dir");
        let log = CaptureLog::open(&db_path, capture_dir).unwrap();
        seed_query_fixture(&log).await;

        let by_source = log
            .query(CaptureQueryFilter {
                source: Some("scheduler".to_owned()),
                limit: 10,
                ..Default::default()
            })
            .await;
        assert_eq!(by_source.total, 3);

        let by_profile = log
            .query(CaptureQueryFilter {
                profile: Some("master_archive".to_owned()),
                limit: 10,
                ..Default::default()
            })
            .await;
        assert_eq!(by_profile.total, 2);

        let by_success = log
            .query(CaptureQueryFilter {
                success: Some(false),
                limit: 10,
                ..Default::default()
            })
            .await;
        assert_eq!(by_success.total, 1);
        assert!(
            by_success.entries[0]
                .capture_id
                .starts_with("scheduler-master-archive-failed-"),
            "got {}",
            by_success.entries[0].capture_id
        );
    }

    /// A rule slug that's a substring of another rule's slug ("dawn" vs.
    /// "dawn-2") must not false-match via the padded `LIKE` filter.
    #[tokio::test]
    async fn query_filters_by_rule_slug_without_substring_false_matches() {
        let db_path = unique_temp_dir("query-rule-slug-db").join("history.db");
        let capture_dir = unique_temp_dir("query-rule-slug-capture-dir");
        let log = CaptureLog::open(&db_path, capture_dir).unwrap();
        seed_query_fixture(&log).await;

        let dawn = log
            .query(CaptureQueryFilter {
                rule_slug: Some("dawn".to_owned()),
                limit: 10,
                ..Default::default()
            })
            .await;
        assert_eq!(dawn.total, 1);
        assert_eq!(dawn.entries[0].triggered_by, vec!["dawn".to_owned()]);

        let dawn_2 = log
            .query(CaptureQueryFilter {
                rule_slug: Some("dawn-2".to_owned()),
                limit: 10,
                ..Default::default()
            })
            .await;
        assert_eq!(dawn_2.total, 1);
        assert_eq!(dawn_2.entries[0].triggered_by, vec!["dawn-2".to_owned()]);
    }

    #[tokio::test]
    async fn query_paginates_newest_first_with_a_total_independent_of_limit() {
        let db_path = unique_temp_dir("query-page-db").join("history.db");
        let capture_dir = unique_temp_dir("query-page-capture-dir");
        let log = CaptureLog::open(&db_path, capture_dir).unwrap();
        seed_query_fixture(&log).await;

        let page1 = log
            .query(CaptureQueryFilter {
                limit: 2,
                offset: 0,
                ..Default::default()
            })
            .await;
        assert_eq!(
            page1.total, 4,
            "total must reflect all matching rows, not just this page"
        );
        assert_eq!(page1.entries.len(), 2);

        let page2 = log
            .query(CaptureQueryFilter {
                limit: 2,
                offset: 2,
                ..Default::default()
            })
            .await;
        assert_eq!(page2.total, 4);
        assert_eq!(page2.entries.len(), 2);

        let page1_ids: Vec<_> = page1.entries.iter().map(|e| &e.capture_id).collect();
        let page2_ids: Vec<_> = page2.entries.iter().map(|e| &e.capture_id).collect();
        assert!(
            page1_ids.iter().all(|id| !page2_ids.contains(id)),
            "pages must not overlap"
        );
    }

    #[tokio::test]
    async fn query_filters_by_captured_at_date_range() {
        let db_path = unique_temp_dir("query-range-db").join("history.db");
        let capture_dir = unique_temp_dir("query-range-capture-dir");
        let log = CaptureLog::open(&db_path, capture_dir).unwrap();

        {
            let connection = log.inner.db.lock().unwrap();
            connection.execute(
                "INSERT INTO captures (capture_id, captured_at, source, profile, save_dng, success, duration_ms, bytes_total, error, detail_json, triggered_by)
                 VALUES ('old', 1758153600, 'web_ui', 'master_archive', 1, 1, 1000, 5000, NULL, '{}', ',,')",
                [],
            ).unwrap();
            connection.execute(
                "INSERT INTO captures (capture_id, captured_at, source, profile, save_dng, success, duration_ms, bytes_total, error, detail_json, triggered_by)
                 VALUES ('new', 1758240000, 'web_ui', 'master_archive', 1, 1, 1000, 5000, NULL, '{}', ',,')",
                [],
            ).unwrap();
        }

        let since_new = log
            .query(CaptureQueryFilter {
                since_unix_ms: Some(1758240000 * 1000),
                limit: 10,
                ..Default::default()
            })
            .await;
        assert_eq!(since_new.total, 1);

        let until_old = log
            .query(CaptureQueryFilter {
                until_unix_ms: Some(1758153600 * 1000),
                limit: 10,
                ..Default::default()
            })
            .await;
        assert_eq!(until_old.total, 1);
    }

    #[tokio::test]
    async fn window_rows_returns_small_columns_inside_the_half_open_window() {
        let dir = unique_temp_dir("window-rows");
        let log = CaptureLog::open(&dir.join("history.db"), dir.clone()).expect("open");
        {
            let connection = log.inner.db.lock().unwrap();
            for (id, at, source, success, bytes, error) in [
                ("a", 99, "scheduler", true, 10, None),
                ("b", 100, "scheduler", true, 20, None),
                ("c", 150, "web_ui", true, 30, None),
                ("d", 160, "scheduler", false, 0, Some("camera timeout")),
                ("e", 200, "scheduler", true, 40, None),
            ] {
                connection
                    .execute(
                        "INSERT INTO captures (capture_id, captured_at, source, profile, save_dng,
                         success, duration_ms, bytes_total, error, detail_json)
                         VALUES (?1, ?2, ?3, 'binning_2k', 0, ?4, 1, ?5, ?6, '{}')",
                        rusqlite::params![id, at, source, success, bytes, error],
                    )
                    .unwrap();
            }
        }
        let rows = log.window_rows(100, 200).await;
        let ids: Vec<i64> = rows.iter().map(|row| row.captured_at_unix).collect();
        assert_eq!(ids, vec![100, 150, 160]);
        assert_eq!(rows[1].source, "web_ui");
        assert_eq!(rows[2].error.as_deref(), Some("camera timeout"));
        assert!(!rows[2].success);
        assert_eq!(rows[0].bytes_total, 20);
        std::fs::remove_dir_all(&dir).ok();
    }
}
