keefo/optic/src/optic_alerts.rs

//! In-daemon health alerts (`docs/optic-daemon-alerts.md`).
//!
//! A passive observer, like `optic_capture_log`: every 30s it reads the
//! scheduler, sync, capture-history, and system-status signals the daemon
//! already has, evaluates a fixed set of failure conditions, and sends one
//! notification when a condition starts, a reminder while it persists, and
//! a recovery notice when it clears. It never changes camera, scheduler, or
//! sync state, and nothing that goes wrong in here (bad config, a failed
//! delivery) affects capture or transfer.
//!
//! Split the same way as `optic_scheduler`: a pure half (`Monitor`,
//! `Debouncer`, `Outbox`, config parsing) that takes an explicit `now` and
//! is unit-tested with a fake clock on macOS, and a small actor
//! (`AlertsHandle`) that gathers real signals and delivers notifications.
//! Delivery shells out to the system `curl` (the same pattern `optic_sync`
//! uses for `ssh`) rather than adding an HTTP client crate.

use std::{
    collections::VecDeque,
    env,
    path::{Path, PathBuf},
    process::Stdio,
    sync::{Arc, LazyLock},
};

use chrono::{DateTime, Duration, NaiveTime, TimeZone as _, Utc};
use chrono_tz::Tz;
use serde::{Deserialize, Serialize};
use serde_json::Value;
use tokio::{
    io::AsyncWriteExt as _,
    process::Command,
    sync::{mpsc, oneshot, watch},
};

use crate::{
    durable_state,
    optic_capture_log::{CaptureLog, CaptureQueryFilter},
    optic_digest::{
        self, CaptureRow, Decision, Digest, DigestInput, DigestState, EventRow, HeartbeatSnapshot,
        Sample, SyncSnapshot,
    },
    optic_events::SystemEventLog,
    optic_heartbeat::{self, ArmedOn, HeartbeatPlan},
    optic_scheduler::{self, LastCapture, ScheduleConfig, ScheduleRunState, SchedulerHandle},
    optic_sync::{DataSyncManager, SyncStatus},
    system_status::SystemStatusReader,
};

pub const POLL_INTERVAL: std::time::Duration = std::time::Duration::from_secs(30);
/// Undelivered notifications kept for retry; the oldest is dropped beyond this.
const OUTBOX_CAPACITY: usize = 32;
/// Scheduled-capture outcomes remembered by the fallback tracker used when
/// the capture history database is unavailable.
const OUTCOME_HISTORY: usize = 16;
/// `capture_stalled` never replays the schedule further back than this, so a
/// long-dead station doesn't make every tick compute days of occurrences.
const STALL_LOOKBACK: Duration = Duration::hours(24);
const CURL_TIMEOUT_SECS: u64 = 10;
const DEFAULT_NTFY_SERVER: &str = "https://ntfy.sh";
const DEFAULT_CONFIG_RELATIVE_PATH: &str = ".config/optic-daemon/alerts.json";

// ---------------------------------------------------------------------------
// Conditions and thresholds
// ---------------------------------------------------------------------------

#[derive(Debug, Clone, Copy, PartialEq, Eq, Serialize)]
#[serde(rename_all = "snake_case")]
pub enum Condition {
    CaptureStalled,
    CaptureOverdue,
    CaptureFailing,
    SyncBacklog,
    CaptureTmpfsLow,
    TemperatureHigh,
    Throttled,
}

impl Condition {
    pub const ALL: [Condition; 7] = [
        Condition::CaptureStalled,
        Condition::CaptureOverdue,
        Condition::CaptureFailing,
        Condition::SyncBacklog,
        Condition::CaptureTmpfsLow,
        Condition::TemperatureHigh,
        Condition::Throttled,
    ];

    fn index(self) -> usize {
        self as usize
    }

    fn title(self) -> &'static str {
        match self {
            Self::CaptureStalled => "captures stalled",
            Self::CaptureOverdue => "scheduled capture overdue",
            Self::CaptureFailing => "captures failing",
            Self::SyncBacklog => "sync backlog",
            Self::CaptureTmpfsLow => "capture tmpfs low",
            Self::TemperatureHigh => "CPU temperature high",
            Self::Throttled => "throttled / under-voltage",
        }
    }
}

/// Defaults are the "Balanced" preset confirmed on 2026-09-20 (design doc
/// §5). Every field is optional in `alerts.json`; unknown fields are
/// rejected so a misspelt override is reported instead of ignored.
#[derive(Debug, Clone, PartialEq, Serialize, Deserialize)]
#[serde(default, deny_unknown_fields)]
pub struct Thresholds {
    pub capture_stalled_after_secs: u64,
    pub capture_overdue_after_secs: u64,
    pub capture_failures_in_a_row: u32,
    pub sync_backlog_after_secs: u64,
    pub tmpfs_low_fire_below_percent: f64,
    pub tmpfs_low_clear_above_percent: f64,
    pub temperature_fire_at_celsius: f32,
    pub temperature_clear_below_celsius: f32,
    /// How long `temperature_high` and `throttled` must hold before firing.
    pub sustained_secs: u64,
    pub recover_after_secs: u64,
    pub repeat_every_secs: u64,
}

impl Default for Thresholds {
    fn default() -> Self {
        Self {
            capture_stalled_after_secs: 15 * 60,
            capture_overdue_after_secs: 5 * 60,
            capture_failures_in_a_row: 3,
            sync_backlog_after_secs: 30 * 60,
            tmpfs_low_fire_below_percent: 25.0,
            tmpfs_low_clear_above_percent: 35.0,
            temperature_fire_at_celsius: 80.0,
            temperature_clear_below_celsius: 75.0,
            sustained_secs: 5 * 60,
            recover_after_secs: 5 * 60,
            repeat_every_secs: 6 * 3600,
        }
    }
}

impl Thresholds {
    fn fire_after(&self, condition: Condition) -> Duration {
        match condition {
            Condition::TemperatureHigh | Condition::Throttled => secs(self.sustained_secs),
            _ => Duration::zero(),
        }
    }

    fn timing(&self, condition: Condition) -> Timing {
        Timing {
            fire_after: self.fire_after(condition),
            recover_after: secs(self.recover_after_secs),
            repeat_every: secs(self.repeat_every_secs),
        }
    }

    fn warnings(&self) -> Vec<String> {
        let mut warnings = Vec::new();
        if self.tmpfs_low_clear_above_percent < self.tmpfs_low_fire_below_percent {
            warnings.push(
                "tmpfs_low_clear_above_percent is below tmpfs_low_fire_below_percent; the alert may flap"
                    .to_owned(),
            );
        }
        if self.temperature_clear_below_celsius > self.temperature_fire_at_celsius {
            warnings.push(
                "temperature_clear_below_celsius is above temperature_fire_at_celsius; the alert may flap"
                    .to_owned(),
            );
        }
        let durations = [
            self.capture_stalled_after_secs,
            self.capture_overdue_after_secs,
            self.sync_backlog_after_secs,
            self.sustained_secs,
            self.recover_after_secs,
            self.repeat_every_secs,
        ];
        if durations.iter().any(|&value| value > MAX_THRESHOLD_SECS) {
            warnings.push(format!(
                "durations above {MAX_THRESHOLD_SECS}s (30 days) are clamped to 30 days"
            ));
        }
        if self.repeat_every_secs == 0 {
            warnings.push("repeat_every_secs is 0; reminders are disabled".to_owned());
        }
        warnings
    }
}

/// Threshold durations are clamped to this so an absurd config value can't
/// overflow `DateTime` arithmetic (release builds use `panic = "abort"`, so
/// an overflow panic here would take the whole daemon down).
const MAX_THRESHOLD_SECS: u64 = 30 * 24 * 3600;

fn secs(value: u64) -> Duration {
    Duration::seconds(value.min(MAX_THRESHOLD_SECS) as i64)
}

// ---------------------------------------------------------------------------
// Debounce state machine (pure; design doc §5 "Debounce, recovery, repeat")
// ---------------------------------------------------------------------------

#[derive(Debug, Clone, Copy)]
struct Timing {
    fire_after: Duration,
    recover_after: Duration,
    /// Zero disables reminders.
    repeat_every: Duration,
}

#[derive(Debug, Clone, Copy, PartialEq)]
enum Phase {
    Clear,
    Pending {
        since: DateTime<Utc>,
    },
    Firing {
        since: DateTime<Utc>,
        last_notified: DateTime<Utc>,
    },
    Recovering {
        since: DateTime<Utc>,
        clear_since: DateTime<Utc>,
        last_notified: DateTime<Utc>,
    },
}

#[derive(Debug, Clone, Copy, PartialEq, Eq, Serialize)]
#[serde(rename_all = "snake_case")]
pub enum Transition {
    Fired,
    Reminder,
    Resolved,
}

impl Transition {
    fn label(self) -> &'static str {
        match self {
            Self::Fired => "FIRING",
            Self::Reminder => "STILL FIRING",
            Self::Resolved => "RESOLVED",
        }
    }
}

#[derive(Debug, Clone, Copy)]
struct Debouncer {
    phase: Phase,
}

impl Debouncer {
    fn new() -> Self {
        Self {
            phase: Phase::Clear,
        }
    }

    /// Advances one tick. `active = None` means the signal was unavailable:
    /// nothing changes, so an unknown signal neither fires nor resolves.
    /// Returns the onset time alongside any notification to send.
    fn step(
        &mut self,
        active: Option<bool>,
        now: DateTime<Utc>,
        timing: Timing,
    ) -> Option<(Transition, DateTime<Utc>)> {
        let active = active?;
        let reminder_due = |last_notified: DateTime<Utc>| {
            timing.repeat_every > Duration::zero() && now - last_notified >= timing.repeat_every
        };
        match (self.phase, active) {
            (Phase::Clear, false) => None,
            (Phase::Clear, true) => {
                self.phase = Phase::Pending { since: now };
                self.fire_if_due(now, timing)
            }
            (Phase::Pending { .. }, true) => self.fire_if_due(now, timing),
            (Phase::Pending { .. }, false) => {
                self.phase = Phase::Clear;
                None
            }
            // Still active, or flapped back while Recovering before
            // `recover_after` elapsed: (back to) Firing with no new FIRING
            // notification, only a reminder if one is due.
            (
                Phase::Firing {
                    since,
                    last_notified,
                }
                | Phase::Recovering {
                    since,
                    last_notified,
                    ..
                },
                true,
            ) => {
                let remind = reminder_due(last_notified);
                self.phase = Phase::Firing {
                    since,
                    last_notified: if remind { now } else { last_notified },
                };
                remind.then_some((Transition::Reminder, since))
            }
            (
                Phase::Firing {
                    since,
                    last_notified,
                },
                false,
            ) => {
                self.phase = Phase::Recovering {
                    since,
                    clear_since: now,
                    last_notified,
                };
                self.resolve_if_due(now, timing)
            }
            (
                Phase::Recovering {
                    since,
                    clear_since,
                    last_notified,
                },
                false,
            ) => {
                if let Some(event) = self.resolve_if_due(now, timing) {
                    return Some(event);
                }
                if reminder_due(last_notified) {
                    self.phase = Phase::Recovering {
                        since,
                        clear_since,
                        last_notified: now,
                    };
                    return Some((Transition::Reminder, since));
                }
                None
            }
        }
    }

    fn fire_if_due(
        &mut self,
        now: DateTime<Utc>,
        timing: Timing,
    ) -> Option<(Transition, DateTime<Utc>)> {
        let Phase::Pending { since } = self.phase else {
            return None;
        };
        if now - since < timing.fire_after {
            return None;
        }
        self.phase = Phase::Firing {
            since,
            last_notified: now,
        };
        Some((Transition::Fired, since))
    }

    fn resolve_if_due(
        &mut self,
        now: DateTime<Utc>,
        timing: Timing,
    ) -> Option<(Transition, DateTime<Utc>)> {
        let Phase::Recovering {
            since, clear_since, ..
        } = self.phase
        else {
            return None;
        };
        if now - clear_since < timing.recover_after {
            return None;
        }
        self.phase = Phase::Clear;
        Some((Transition::Resolved, since))
    }
}

// ---------------------------------------------------------------------------
// Observations and condition evaluation (pure)
// ---------------------------------------------------------------------------

/// One scheduled capture's result, newest first in `Observation`.
#[derive(Debug, Clone, PartialEq)]
pub struct Outcome {
    pub at: DateTime<Utc>,
    pub success: bool,
    pub error: Option<String>,
}

#[derive(Debug, Clone, PartialEq)]
pub struct SyncObservation {
    pub enabled: bool,
    pub paused: bool,
    pub queued_files: u64,
    pub queued_bytes: u64,
    pub transferred_files: u64,
    pub last_error: Option<String>,
}

/// Everything one evaluation tick needs, gathered by the actor (or built
/// directly by tests). `None` fields mean "signal unavailable this tick".
#[derive(Debug, Clone)]
pub struct Observation {
    pub now: DateTime<Utc>,
    pub scheduler_running: bool,
    pub next_capture_at: Option<DateTime<Utc>>,
    /// The committed schedule, replayed over a past window by
    /// `capture_stalled` to find shots that should have fired.
    pub schedule: ScheduleConfig,
    /// Most recent scheduled-capture outcomes, newest first.
    pub recent_outcomes: Vec<Outcome>,
    pub last_success_at: Option<DateTime<Utc>>,
    pub sync: Option<SyncObservation>,
    /// `(total_bytes, available_bytes)` of the capture tmpfs.
    pub capture_disk: Option<(u64, u64)>,
    pub cpu_temp_celsius: Option<f32>,
    /// Raw `vcgencmd get_throttled` bit field.
    pub throttled: Option<u32>,
}

#[derive(Debug, Clone, PartialEq)]
pub struct Notification {
    pub condition: Condition,
    pub transition: Transition,
    pub at: DateTime<Utc>,
    /// When the condition started (onset of Pending).
    pub since: DateTime<Utc>,
    pub detail: String,
}

impl Notification {
    fn title(&self, station_name: Option<&str>) -> String {
        let station = station_name
            .map(|name| format!(" {name}"))
            .unwrap_or_default();
        format!(
            "Optic{station}: {} {}",
            self.transition.label(),
            self.condition.title()
        )
    }

    fn message(&self) -> String {
        match self.transition {
            Transition::Resolved => format!(
                "{}\nWas active since {} ({}).",
                self.detail,
                format_time(self.since),
                format_duration(self.at - self.since)
            ),
            Transition::Fired | Transition::Reminder => format!(
                "{}\nActive since {} ({}).",
                self.detail,
                format_time(self.since),
                format_duration(self.at - self.since)
            ),
        }
    }
}

#[derive(Debug, Clone)]
struct Tracker {
    debouncer: Debouncer,
    /// Last known raw evaluation, for hysteresis. Unchanged by unknown ticks.
    raw_active: bool,
    detail: Option<String>,
}

#[derive(Debug, Clone, Copy)]
struct Backlog {
    since: DateTime<Utc>,
    transferred_files: u64,
}

/// Pure monitor state. Feed it one `Observation` per tick; it returns the
/// notifications to send.
pub struct Monitor {
    thresholds: Thresholds,
    started_at: DateTime<Utc>,
    /// When the scheduler was last seen switching to Running (or the
    /// monitor start if it was already running). Shots due before this are
    /// never blamed on the station.
    running_since: Option<DateTime<Utc>>,
    backlog: Option<Backlog>,
    trackers: Vec<Tracker>,
    last_evaluated_at: Option<DateTime<Utc>>,
}

impl Monitor {
    pub fn new(thresholds: Thresholds, started_at: DateTime<Utc>) -> Self {
        Self {
            thresholds,
            started_at,
            running_since: None,
            backlog: None,
            trackers: vec![
                Tracker {
                    debouncer: Debouncer::new(),
                    raw_active: false,
                    detail: None,
                };
                Condition::ALL.len()
            ],
            last_evaluated_at: None,
        }
    }

    pub fn observe(&mut self, obs: &Observation) -> Vec<Notification> {
        self.update_run_state(obs);
        self.update_backlog(obs);
        let mut notifications = Vec::new();
        for condition in Condition::ALL {
            let evaluation = self.evaluate(condition, obs);
            let timing = self.thresholds.timing(condition);
            let tracker = &mut self.trackers[condition.index()];
            let active = evaluation.as_ref().map(|(active, _)| *active);
            if let Some((active, detail)) = evaluation {
                tracker.raw_active = active;
                tracker.detail = Some(detail);
            }
            if let Some((transition, since)) = tracker.debouncer.step(active, obs.now, timing) {
                notifications.push(Notification {
                    condition,
                    transition,
                    at: obs.now,
                    since,
                    detail: tracker.detail.clone().unwrap_or_default(),
                });
            }
        }
        self.last_evaluated_at = Some(obs.now);
        notifications
    }

    fn update_run_state(&mut self, obs: &Observation) {
        self.running_since = match (self.running_since, obs.scheduler_running) {
            (_, false) => None,
            (Some(since), true) => Some(since),
            // First tick after startup: don't blame shots from before the
            // monitor existed. Later: a pause→resume transition.
            (None, true) if self.last_evaluated_at.is_none() => Some(self.started_at),
            (None, true) => Some(obs.now),
        };
    }

    fn update_backlog(&mut self, obs: &Observation) {
        let Some(sync) = &obs.sync else {
            return;
        };
        if !sync.enabled || sync.paused || sync.queued_files == 0 {
            self.backlog = None;
            return;
        }
        self.backlog = match self.backlog {
            Some(backlog) if backlog.transferred_files == sync.transferred_files => Some(backlog),
            // New backlog, or transfers made progress: restart the clock.
            _ => Some(Backlog {
                since: obs.now,
                transferred_files: sync.transferred_files,
            }),
        };
    }

    /// `None` = signal unavailable. Otherwise `(active, human detail)`.
    fn evaluate(&self, condition: Condition, obs: &Observation) -> Option<(bool, String)> {
        let was_active = self.trackers[condition.index()].raw_active;
        match condition {
            Condition::CaptureStalled => Some(self.capture_stalled(obs)),
            Condition::CaptureOverdue => Some(self.capture_overdue(obs)),
            Condition::CaptureFailing => Some(self.capture_failing(obs)),
            Condition::SyncBacklog => self.sync_backlog(obs),
            Condition::CaptureTmpfsLow => tmpfs_low(&self.thresholds, obs, was_active),
            Condition::TemperatureHigh => temperature_high(&self.thresholds, obs, was_active),
            Condition::Throttled => obs.throttled.map(throttled),
        }
    }

    fn capture_stalled(&self, obs: &Observation) -> (bool, String) {
        let Some(running_since) = self.running_since else {
            return (false, "Scheduler is paused.".to_owned());
        };
        let stall_after = secs(self.thresholds.capture_stalled_after_secs);
        let cutoff = obs.now - stall_after;
        let mut window_start = running_since.max(obs.now - STALL_LOOKBACK);
        if let Some(last_success) = obs.last_success_at {
            if last_success >= cutoff {
                return (
                    false,
                    format!(
                        "Last successful scheduled capture at {}.",
                        format_time(last_success)
                    ),
                );
            }
            window_start = window_start.max(last_success);
        }
        if window_start >= cutoff {
            return (
                false,
                "No scheduled shot has been due long enough to judge.".to_owned(),
            );
        }
        // +1s so a shot exactly at `cutoff` is included regardless of
        // whether the forecast horizon's end is inclusive.
        let missed = optic_scheduler::forecast(
            &obs.schedule,
            window_start,
            cutoff - window_start + Duration::seconds(1),
        )
        .into_iter()
        .map(|shot| shot.at.with_timezone(&Utc))
        .find(|at| *at > window_start && *at <= cutoff);
        match missed {
            Some(due) => {
                let last = obs
                    .last_success_at
                    .map_or_else(|| "none since monitoring started".to_owned(), format_time);
                (
                    true,
                    format!(
                        "A scheduled shot was due at {} and no scheduled capture has succeeded since (last success: {last}).",
                        format_time(due)
                    ),
                )
            }
            None => (false, "No missed scheduled shots.".to_owned()),
        }
    }

    fn capture_overdue(&self, obs: &Observation) -> (bool, String) {
        if self.running_since.is_none() {
            return (false, "Scheduler is paused.".to_owned());
        }
        let overdue_after = secs(self.thresholds.capture_overdue_after_secs);
        match obs.next_capture_at {
            Some(due) if obs.now - due > overdue_after => (
                true,
                format!(
                    "The scheduled capture due at {} has not completed ({} late); the scheduler or camera may be hung.",
                    format_time(due),
                    format_duration(obs.now - due)
                ),
            ),
            Some(due) => (false, format!("Next capture due at {}.", format_time(due))),
            None => (false, "No capture currently due.".to_owned()),
        }
    }

    fn capture_failing(&self, obs: &Observation) -> (bool, String) {
        let Some(running_since) = self.running_since else {
            return (false, "Scheduler is paused.".to_owned());
        };
        let needed = self.thresholds.capture_failures_in_a_row.max(1);
        // Only outcomes since the scheduler last started running count, so
        // a resume (or daemon restart) doesn't re-fire on stale failures.
        let failures: Vec<&Outcome> = obs
            .recent_outcomes
            .iter()
            .take_while(|outcome| outcome.at >= running_since && !outcome.success)
            .collect();
        let count = u32::try_from(failures.len()).unwrap_or(u32::MAX);
        if count >= needed {
            let last_error = failures
                .first()
                .and_then(|outcome| outcome.error.as_deref())
                .unwrap_or("unknown error");
            (
                true,
                format!("The last {count} scheduled captures failed. Last error: {last_error}"),
            )
        } else {
            (
                false,
                format!("{count} consecutive scheduled capture failure(s)."),
            )
        }
    }

    fn sync_backlog(&self, obs: &Observation) -> Option<(bool, String)> {
        let sync = obs.sync.as_ref()?;
        if !sync.enabled {
            return Some((false, "Sync is disabled.".to_owned()));
        }
        if sync.paused {
            return Some((false, "Sync is paused.".to_owned()));
        }
        let Some(backlog) = self.backlog else {
            return Some((false, "Sync queue is empty.".to_owned()));
        };
        let stuck_for = obs.now - backlog.since;
        let active = stuck_for >= secs(self.thresholds.sync_backlog_after_secs);
        let error = sync
            .last_error
            .as_deref()
            .map(|error| format!(" Last error: {error}"))
            .unwrap_or_default();
        Some((
            active,
            format!(
                "{} file(s) ({}) queued with no successful transfer for {}.{error}",
                sync.queued_files,
                format_bytes(sync.queued_bytes),
                format_duration(stuck_for)
            ),
        ))
    }
}

fn tmpfs_low(
    thresholds: &Thresholds,
    obs: &Observation,
    was_active: bool,
) -> Option<(bool, String)> {
    let (total, available) = obs.capture_disk?;
    if total == 0 {
        return None;
    }
    let free_percent = available as f64 * 100.0 / total as f64;
    let active = if was_active {
        free_percent <= thresholds.tmpfs_low_clear_above_percent
    } else {
        free_percent < thresholds.tmpfs_low_fire_below_percent
    };
    Some((
        active,
        format!(
            "Capture tmpfs has {} free of {} ({free_percent:.0}%).",
            format_bytes(available),
            format_bytes(total)
        ),
    ))
}

fn temperature_high(
    thresholds: &Thresholds,
    obs: &Observation,
    was_active: bool,
) -> Option<(bool, String)> {
    let celsius = obs.cpu_temp_celsius?;
    let active = if was_active {
        celsius >= thresholds.temperature_clear_below_celsius
    } else {
        celsius >= thresholds.temperature_fire_at_celsius
    };
    Some((active, format!("CPU temperature is {celsius:.1} °C.")))
}

/// Bits 0–3 of `vcgencmd get_throttled` are the *current* state; bits
/// 16–19 are "has occurred since boot" and are ignored here.
fn throttled(bits: u32) -> (bool, String) {
    const FLAGS: [(u32, &str); 4] = [
        (0x1, "under-voltage"),
        (0x2, "ARM frequency capped"),
        (0x4, "throttled"),
        (0x8, "soft temperature limit"),
    ];
    let current: Vec<&str> = FLAGS
        .iter()
        .filter(|(mask, _)| bits & mask != 0)
        .map(|(_, name)| *name)
        .collect();
    if current.is_empty() {
        (false, format!("Not throttled (get_throttled=0x{bits:x})."))
    } else {
        (
            true,
            format!(
                "Currently {} (get_throttled=0x{bits:x}).",
                current.join(", ")
            ),
        )
    }
}

/// Parses `vcgencmd get_throttled`'s `throttled=0x50005\n` output.
#[cfg_attr(not(target_os = "linux"), allow(dead_code))]
fn parse_throttled(text: &str) -> Option<u32> {
    let hex = text.trim().strip_prefix("throttled=0x")?;
    u32::from_str_radix(hex, 16).ok()
}

fn format_time(time: DateTime<Utc>) -> String {
    time.format("%Y-%m-%d %H:%M:%S UTC").to_string()
}

fn format_duration(duration: Duration) -> String {
    let total = duration.num_seconds().max(0);
    if total < 60 {
        format!("{total}s")
    } else if total < 3600 {
        format!("{}m", total / 60)
    } else {
        format!("{}h {}m", total / 3600, (total % 3600) / 60)
    }
}

fn format_bytes(bytes: u64) -> String {
    format!("{:.1} MiB", bytes as f64 / (1024.0 * 1024.0))
}

// ---------------------------------------------------------------------------
// Scheduled-capture outcome fallback (when the history DB is unavailable)
// ---------------------------------------------------------------------------

/// Remembers each distinct `SchedulerStatus.last_capture` it sees. Only a
/// fallback: polling can miss an outcome that is immediately superseded,
/// which the capture history database does not.
#[derive(Debug, Default)]
struct OutcomeTracker {
    recent: VecDeque<Outcome>,
    last_success_at: Option<DateTime<Utc>>,
}

impl OutcomeTracker {
    fn record(&mut self, last: Option<&LastCapture>) {
        let Some(last) = last else {
            return;
        };
        if self
            .recent
            .front()
            .is_some_and(|newest| newest.at == last.at)
        {
            return;
        }
        if last.success {
            self.last_success_at = Some(last.at);
        }
        self.recent.push_front(Outcome {
            at: last.at,
            success: last.success,
            error: last.error.clone(),
        });
        self.recent.truncate(OUTCOME_HISTORY);
    }
}

// ---------------------------------------------------------------------------
// Outbox (pure)
// ---------------------------------------------------------------------------

#[derive(Debug, Default)]
struct Outbox {
    queue: VecDeque<Notification>,
}

impl Outbox {
    /// Returns `false` if the notification was not queued: a reminder is
    /// redundant while another notification for that condition is waiting.
    fn push(&mut self, notification: Notification) -> bool {
        if notification.transition == Transition::Reminder
            && self
                .queue
                .iter()
                .any(|queued| queued.condition == notification.condition)
        {
            return false;
        }
        if self.queue.len() >= OUTBOX_CAPACITY
            && let Some(dropped) = self.queue.pop_front()
        {
            tracing::warn!(
                condition = ?dropped.condition,
                transition = ?dropped.transition,
                "alert outbox full; dropped the oldest undelivered notification"
            );
        }
        self.queue.push_back(notification);
        true
    }
}

// ---------------------------------------------------------------------------
// Configuration
// ---------------------------------------------------------------------------

#[derive(Clone, PartialEq, Serialize, Deserialize)]
#[serde(deny_unknown_fields)]
pub struct NtfyConfig {
    #[serde(default = "default_ntfy_server")]
    pub server: String,
    pub topic: String,
    #[serde(default, skip_serializing_if = "Option::is_none")]
    pub token: Option<String>,
}

fn default_ntfy_server() -> String {
    DEFAULT_NTFY_SERVER.to_owned()
}

/// The topic on a public server is effectively a password, so neither it
/// nor the token is ever printed.
impl std::fmt::Debug for NtfyConfig {
    fn fmt(&self, f: &mut std::fmt::Formatter<'_>) -> std::fmt::Result {
        f.debug_struct("NtfyConfig")
            .field("server", &self.server)
            .field("topic", &"<redacted>")
            .field("token", &self.token.as_ref().map(|_| "<redacted>"))
            .finish()
    }
}

/// Daily digest settings (`docs/optic-daemon-digest-heartbeat.md` §5.2).
#[derive(Debug, Clone, PartialEq, Serialize, Deserialize)]
#[serde(default, deny_unknown_fields)]
pub struct DigestSettings {
    pub enabled: bool,
    /// `HH:MM`, 24 h, in the Station timezone.
    pub send_at: String,
}

impl Default for DigestSettings {
    fn default() -> Self {
        Self {
            enabled: true,
            send_at: "08:00".to_owned(),
        }
    }
}

/// External heartbeat settings. The section is opt-in: absent means off.
#[derive(Debug, Clone, PartialEq, Serialize, Deserialize)]
#[serde(default, deny_unknown_fields)]
pub struct HeartbeatSettings {
    pub enabled: bool,
    pub interval_secs: u64,
    pub alert_after_secs: u64,
    pub sequence_id: String,
}

impl Default for HeartbeatSettings {
    fn default() -> Self {
        Self {
            enabled: true,
            interval_secs: optic_heartbeat::DEFAULT_INTERVAL_SECS,
            alert_after_secs: optic_heartbeat::DEFAULT_ALERT_AFTER_SECS,
            sequence_id: optic_heartbeat::DEFAULT_SEQUENCE_ID.to_owned(),
        }
    }
}

/// The `notifications` section of `config.json`, and the shape of the
/// legacy `alerts.json` (imported once). Unknown fields are rejected so a
/// misspelt setting is reported rather than ignored. `Debug` is safe: the
/// ntfy topic and token are redacted.
#[derive(Debug, Clone, PartialEq, Serialize, Deserialize)]
#[serde(deny_unknown_fields)]
pub struct NotificationSettings {
    #[serde(default = "default_true")]
    pub enabled: bool,
    #[serde(default, skip_serializing_if = "Option::is_none")]
    pub station_name: Option<String>,
    #[serde(default, skip_serializing_if = "Option::is_none")]
    pub ntfy: Option<NtfyConfig>,
    #[serde(default)]
    pub digest: DigestSettings,
    #[serde(default, skip_serializing_if = "Option::is_none")]
    pub heartbeat: Option<HeartbeatSettings>,
    #[serde(default)]
    pub thresholds: Thresholds,
}

fn default_true() -> bool {
    true
}

/// Settings resolved into something runnable. Always usable: any problem
/// falls back to a dry-run notifier with the reason recorded.
#[derive(Debug, Clone)]
pub struct AlertsSetup {
    notifier: Notifier,
    station_name: Option<String>,
    thresholds: Thresholds,
    digest_send_at: Option<NaiveTime>,
    heartbeat: Option<HeartbeatPlan>,
    config_error: Option<String>,
    config_warnings: Vec<String>,
    /// The parsed settings (with secrets); `None` when missing or invalid.
    settings: Option<NotificationSettings>,
}

/// `OPTIC_ALERTS_CONFIG` overrides the default
/// `~/.config/optic-daemon/alerts.json`, the legacy file that is imported
/// into `config.json` once.
pub fn resolve_config_path() -> PathBuf {
    if let Ok(configured) = env::var("OPTIC_ALERTS_CONFIG") {
        return PathBuf::from(configured);
    }
    let home = env::var("HOME").unwrap_or_else(|_| "/tmp".to_owned());
    PathBuf::from(home).join(DEFAULT_CONFIG_RELATIVE_PATH)
}

/// Reads the legacy `alerts.json`. Never fails; a missing file is normal
/// once it has been imported.
pub fn load_config(path: &Path) -> AlertsSetup {
    let setup = match std::fs::read_to_string(path) {
        Ok(content) => {
            let mut setup = parse_config(&content);
            if let Some(warning) = permission_warning(path) {
                setup.config_warnings.push(warning);
            }
            setup
        }
        Err(error) if error.kind() == std::io::ErrorKind::NotFound => dry_run_setup(
            "no notification settings (alerts config file not found); notifications are logged only (dry run)",
        ),
        Err(error) => dry_run_setup(&format!(
            "alerts config file unreadable ({}); notifications are logged only (dry run)",
            error.kind()
        )),
    };
    if setup.settings.is_none()
        && let Some(error) = &setup.config_error
        && !error.contains("not found")
    {
        tracing::warn!(path = %path.display(), %error, "legacy alerts config not usable");
    }
    setup
}

fn dry_run_setup(reason: &str) -> AlertsSetup {
    AlertsSetup {
        notifier: Notifier::DryRun,
        station_name: None,
        thresholds: Thresholds::default(),
        digest_send_at: None,
        heartbeat: None,
        config_error: Some(reason.to_owned()),
        config_warnings: Vec::new(),
        settings: None,
    }
}

fn parse_config(content: &str) -> AlertsSetup {
    match serde_json::from_str::<NotificationSettings>(content) {
        Ok(settings) => resolve(&settings),
        // serde_json's message names the field/line, never echoes values
        // of other fields, so it is safe to surface.
        Err(error) => dry_run_setup(&format!(
            "notification settings are invalid ({error}); notifications are logged only (dry run)"
        )),
    }
}

/// Lenient resolution for settings read from disk: out-of-range values are
/// clamped or switched off with a warning rather than rejected.
fn resolve(settings: &NotificationSettings) -> AlertsSetup {
    let mut warnings = settings.thresholds.warnings();
    let digest_send_at = if settings.digest.enabled {
        let parsed = optic_digest::parse_send_at(&settings.digest.send_at);
        if parsed.is_none() {
            warnings.push("digest.send_at must be HH:MM (24 h); the digest is off".to_owned());
        }
        parsed
    } else {
        None
    };
    let heartbeat = settings
        .heartbeat
        .as_ref()
        .filter(|heartbeat| heartbeat.enabled)
        .and_then(|heartbeat| match heartbeat_plan(heartbeat, &mut warnings) {
            Ok(plan) => Some(plan),
            Err(error) => {
                warnings.push(format!("{error}; the heartbeat is off"));
                None
            }
        });
    let base = |notifier, config_error| AlertsSetup {
        notifier,
        station_name: settings.station_name.clone(),
        thresholds: settings.thresholds.clone(),
        digest_send_at,
        heartbeat: heartbeat.clone(),
        config_error,
        config_warnings: Vec::new(),
        settings: Some(settings.clone()),
    };
    if !settings.enabled {
        let mut setup = base(Notifier::DryRun, None);
        setup.config_warnings = warnings;
        return setup;
    }
    let Some(mut ntfy) = settings.ntfy.clone() else {
        return base(
            Notifier::DryRun,
            Some(
                "notification settings have no \"ntfy\" section; notifications are logged only (dry run)"
                    .to_owned(),
            ),
        );
    };
    ntfy.server = ntfy.server.trim_end_matches('/').to_owned();
    if let Err(error) = validate_ntfy(&ntfy) {
        return base(
            Notifier::DryRun,
            Some(format!("{error}; notifications are logged only (dry run)")),
        );
    }
    if ntfy.server.starts_with("http://") && ntfy.token.is_some() {
        warnings
            .push("ntfy server uses plain http; the access token is sent unencrypted".to_owned());
    }
    let mut setup = base(
        Notifier::Ntfy(NtfySender {
            config: ntfy,
            curl: PathBuf::from("curl"),
        }),
        None,
    );
    setup.config_warnings = warnings;
    setup
}

fn heartbeat_plan(
    heartbeat: &HeartbeatSettings,
    warnings: &mut Vec<String>,
) -> Result<HeartbeatPlan, String> {
    use optic_heartbeat::{
        MAX_ALERT_AFTER_SECS, MAX_INTERVAL_SECS, MIN_ALERT_AFTER_SECS, MIN_ALERT_MARGIN_SECS,
        MIN_INTERVAL_SECS,
    };
    if !optic_heartbeat::valid_sequence_id(&heartbeat.sequence_id) {
        return Err(
            "heartbeat.sequence_id must be 1-64 characters of A-Z, a-z, 0-9, '-' or '_'".to_owned(),
        );
    }
    let interval = heartbeat
        .interval_secs
        .clamp(MIN_INTERVAL_SECS, MAX_INTERVAL_SECS);
    let alert_after = heartbeat
        .alert_after_secs
        .clamp(MIN_ALERT_AFTER_SECS, MAX_ALERT_AFTER_SECS);
    if interval != heartbeat.interval_secs || alert_after != heartbeat.alert_after_secs {
        warnings.push(format!(
            "heartbeat interval must be {MIN_INTERVAL_SECS}-{MAX_INTERVAL_SECS} s and alert delay {MIN_ALERT_AFTER_SECS}-{MAX_ALERT_AFTER_SECS} s; clamped"
        ));
    }
    if alert_after < interval + MIN_ALERT_MARGIN_SECS {
        warnings.push(format!(
            "heartbeat.alert_after_secs should be at least interval_secs + {MIN_ALERT_MARGIN_SECS}; one late check-in may false-alarm"
        ));
    }
    Ok(HeartbeatPlan {
        interval: Duration::seconds(interval as i64),
        alert_after: Duration::seconds(alert_after as i64),
        sequence_id: heartbeat.sequence_id.clone(),
    })
}

/// Strict validation for a save from the Config page: anything out of range
/// is rejected with a reason instead of clamped.
pub fn validate_for_save(settings: &NotificationSettings) -> Result<(), String> {
    use optic_heartbeat::{
        MAX_ALERT_AFTER_SECS, MAX_INTERVAL_SECS, MIN_ALERT_AFTER_SECS, MIN_ALERT_MARGIN_SECS,
        MIN_INTERVAL_SECS,
    };
    if let Some(name) = &settings.station_name
        && (name.is_empty() || name.chars().count() > 64 || name.chars().any(char::is_control))
    {
        return Err("station name must be 1-64 characters without control characters".to_owned());
    }
    match &settings.ntfy {
        Some(ntfy) => validate_ntfy(ntfy)?,
        None if settings.enabled => {
            return Err("an ntfy topic is required to turn notifications on".to_owned());
        }
        None => {}
    }
    if optic_digest::parse_send_at(&settings.digest.send_at).is_none() {
        return Err("digest send time must be HH:MM (24 h)".to_owned());
    }
    if let Some(heartbeat) = &settings.heartbeat {
        if !optic_heartbeat::valid_sequence_id(&heartbeat.sequence_id) {
            return Err(
                "heartbeat sequence ID must be 1-64 characters of A-Z, a-z, 0-9, '-' or '_'"
                    .to_owned(),
            );
        }
        if !(MIN_INTERVAL_SECS..=MAX_INTERVAL_SECS).contains(&heartbeat.interval_secs) {
            return Err(format!(
                "heartbeat interval must be {}-{} minutes",
                MIN_INTERVAL_SECS / 60,
                MAX_INTERVAL_SECS / 60
            ));
        }
        if !(MIN_ALERT_AFTER_SECS..=MAX_ALERT_AFTER_SECS).contains(&heartbeat.alert_after_secs) {
            return Err(format!(
                "heartbeat alert delay must be {} minutes to {} days",
                MIN_ALERT_AFTER_SECS / 60,
                MAX_ALERT_AFTER_SECS / 86_400
            ));
        }
        if heartbeat.alert_after_secs < heartbeat.interval_secs + MIN_ALERT_MARGIN_SECS {
            return Err(format!(
                "heartbeat alert delay must be at least the interval plus {} minutes",
                MIN_ALERT_MARGIN_SECS / 60
            ));
        }
    }
    Ok(())
}

fn validate_ntfy(ntfy: &NtfyConfig) -> Result<(), String> {
    let valid_topic = !ntfy.topic.is_empty()
        && ntfy.topic.len() <= 64
        && ntfy
            .topic
            .chars()
            .all(|c| c.is_ascii_alphanumeric() || c == '-' || c == '_');
    if !valid_topic {
        return Err("ntfy.topic must be 1-64 characters of A-Z, a-z, 0-9, '-' or '_'".to_owned());
    }
    let valid_server = (ntfy.server.starts_with("https://") || ntfy.server.starts_with("http://"))
        && ntfy
            .server
            .chars()
            .all(|c| c.is_ascii_graphic() && c != '"' && c != '\\');
    if !valid_server {
        return Err("ntfy.server must be an http(s):// URL".to_owned());
    }
    // '*' is excluded so a masked token (`tk_a****wxyz`) can never be saved
    // back; real ntfy tokens are `tk_` plus letters and digits.
    if let Some(token) = &ntfy.token
        && (token.is_empty() || !token.chars().all(|c| c.is_ascii_graphic() && c != '*'))
    {
        return Err(
            "ntfy.token must be non-empty printable ASCII without spaces or '*'".to_owned(),
        );
    }
    Ok(())
}

#[cfg(unix)]
fn permission_warning(path: &Path) -> Option<String> {
    use std::os::unix::fs::PermissionsExt as _;
    let mode = std::fs::metadata(path).ok()?.permissions().mode();
    (mode & 0o077 != 0).then(|| {
        format!(
            "alerts config file is accessible by group/others (mode {:o}); chmod 600 it",
            mode & 0o777
        )
    })
}

#[cfg(not(unix))]
fn permission_warning(_path: &Path) -> Option<String> {
    None
}

// ---------------------------------------------------------------------------
// Settings in config.json: masking, view, update, save
// ---------------------------------------------------------------------------

/// Paths of the global config: committed (durable + tmpfs mirror) and the
/// staging copy the dashboard's stage/commit flow uses.
#[derive(Debug, Clone)]
pub struct ConfigPaths {
    pub config_path: PathBuf,
    pub config_cache_path: PathBuf,
    pub preview_config_path: PathBuf,
}

/// Serializes read-modify-write saves of the `notifications` section (the
/// Config page and the one-time import).
static SAVE_LOCK: LazyLock<tokio::sync::Mutex<()>> = LazyLock::new(|| tokio::sync::Mutex::new(()));

/// Masks the ntfy topic and token in a `notifications` value before it is
/// served (`GET /api/status`). Any `topic`/`token` key at any depth is
/// masked, so even a hand-edited, misshapen section cannot leak. The masks
/// contain `****`, which topic and token validation reject, so a masked
/// value can never be saved back as a real secret.
pub fn redact_notifications(value: &mut Value) {
    match value {
        Value::Object(map) => {
            for (key, entry) in map.iter_mut() {
                match (key.as_str(), &*entry) {
                    ("topic" | "token", Value::String(secret)) => {
                        *entry = Value::String(mask_secret(secret));
                    }
                    ("token", Value::Null) => {}
                    ("topic" | "token", _) => *entry = Value::String(SECRET_MASK.to_owned()),
                    _ => redact_notifications(entry),
                }
            }
        }
        Value::Array(items) => items.iter_mut().for_each(redact_notifications),
        _ => {}
    }
}

const SECRET_MASK: &str = "****";
/// Secrets shorter than this are masked completely, so at least 8
/// characters always stay hidden.
const MIN_PARTLY_SHOWN_SECRET: usize = 16;

/// First 4 and last 4 characters with `****` between (`opti****a7f3`),
/// enough to recognise which secret is set. A generated topic (`optic-` +
/// 24 random characters) keeps 22 random characters hidden.
fn mask_secret(secret: &str) -> String {
    let count = secret.chars().count();
    if count < MIN_PARTLY_SHOWN_SECRET {
        return SECRET_MASK.to_owned();
    }
    let head: String = secret.chars().take(4).collect();
    let tail: String = secret.chars().skip(count - 4).collect();
    format!("{head}{SECRET_MASK}{tail}")
}

/// What the Config page sees: never the topic or token themselves.
#[derive(Debug, Clone, Serialize)]
pub struct NotificationsView {
    /// `config` (config.json), `alerts_file` (legacy file, import pending),
    /// or `none`.
    pub source: &'static str,
    pub enabled: bool,
    pub station_name: Option<String>,
    pub server: String,
    pub topic_set: bool,
    /// Masked (`opti****a7f3`), never the topic itself.
    pub topic_hint: Option<String>,
    pub token_set: bool,
    /// Masked like `topic_hint`.
    pub token_hint: Option<String>,
    pub digest: DigestSettings,
    pub heartbeat: HeartbeatSettings,
    /// Why the saved settings cannot be used, if they cannot.
    pub error: Option<String>,
}

impl NotificationsView {
    fn new(source: &'static str, settings: Result<&NotificationSettings, &str>) -> Self {
        let error = settings.err().map(str::to_owned);
        let settings = settings.ok();
        let ntfy = settings.and_then(|settings| settings.ntfy.as_ref());
        Self {
            source,
            enabled: settings.is_some_and(|settings| settings.enabled),
            station_name: settings.and_then(|settings| settings.station_name.clone()),
            server: ntfy.map_or_else(default_ntfy_server, |ntfy| ntfy.server.clone()),
            topic_set: ntfy.is_some(),
            topic_hint: ntfy.map(|ntfy| mask_secret(&ntfy.topic)),
            token_set: ntfy.is_some_and(|ntfy| ntfy.token.is_some()),
            token_hint: ntfy.and_then(|ntfy| ntfy.token.as_deref()).map(mask_secret),
            digest: settings
                .map_or_else(DigestSettings::default, |settings| settings.digest.clone()),
            heartbeat: settings
                .and_then(|settings| settings.heartbeat.clone())
                .unwrap_or(HeartbeatSettings {
                    enabled: false,
                    ..HeartbeatSettings::default()
                }),
            error,
        }
    }
}

/// A save from the Config page. An absent or empty `topic`/`token` keeps
/// the current one; `clear_topic`/`clear_token` remove it (the page sends
/// these when a field that showed a saved value is cleared). Removing the
/// topic removes the whole ntfy channel, token included.
#[derive(Debug, Deserialize)]
#[serde(deny_unknown_fields)]
pub struct NotificationsUpdate {
    pub enabled: bool,
    #[serde(default)]
    pub station_name: Option<String>,
    #[serde(default)]
    pub server: Option<String>,
    #[serde(default)]
    pub topic: Option<String>,
    #[serde(default)]
    pub token: Option<String>,
    #[serde(default)]
    pub clear_topic: bool,
    #[serde(default)]
    pub clear_token: bool,
    pub digest: DigestSettings,
    pub heartbeat: HeartbeatSettings,
}

#[derive(Debug, Clone, PartialEq)]
pub enum SaveError {
    Invalid(String),
    Io(String),
}

fn non_empty(value: Option<&str>) -> Option<String> {
    value
        .map(str::trim)
        .filter(|value| !value.is_empty())
        .map(str::to_owned)
}

/// Merges an update into the current settings (pure). Thresholds are not
/// edited in the UI and are always kept.
fn merge_update(
    current: Option<&NotificationSettings>,
    update: NotificationsUpdate,
) -> NotificationSettings {
    let current_ntfy = current.and_then(|current| current.ntfy.as_ref());
    let server = non_empty(update.server.as_deref())
        .map(|server| server.trim_end_matches('/').to_owned())
        .or_else(|| current_ntfy.map(|ntfy| ntfy.server.clone()))
        .unwrap_or_else(default_ntfy_server);
    let topic = if update.clear_topic {
        None
    } else {
        non_empty(update.topic.as_deref()).or_else(|| current_ntfy.map(|ntfy| ntfy.topic.clone()))
    };
    let token = if update.clear_token {
        None
    } else {
        non_empty(update.token.as_deref())
            .or_else(|| current_ntfy.and_then(|ntfy| ntfy.token.clone()))
    };
    NotificationSettings {
        enabled: update.enabled,
        station_name: non_empty(update.station_name.as_deref()),
        ntfy: topic.map(|topic| NtfyConfig {
            server,
            topic,
            token,
        }),
        digest: update.digest,
        // Kept even when off, so the values are remembered.
        heartbeat: Some(update.heartbeat),
        thresholds: current.map_or_else(Thresholds::default, |current| current.thresholds.clone()),
    }
}

async fn read_committed(cache_path: &Path) -> Option<Value> {
    let content = durable_state::read_cached(cache_path).await.ok()?;
    serde_json::from_str(&content).ok()
}

fn notifications_of(config: &Value) -> Option<&Value> {
    config.get("notifications").filter(|value| !value.is_null())
}

/// The settings in effect: `config.json`'s section if present, else the
/// legacy file (only until it is imported), else none.
fn effective_settings(
    config: Option<&Value>,
    legacy: &AlertsSetup,
) -> (&'static str, Result<NotificationSettings, String>) {
    if let Some(section) = config.and_then(notifications_of) {
        return (
            "config",
            serde_json::from_value(section.clone()).map_err(|error| {
                format!(
                    "notification settings in config.json are invalid ({error}); notifications are logged only (dry run)"
                )
            }),
        );
    }
    match &legacy.settings {
        Some(settings) => ("alerts_file", Ok(settings.clone())),
        None => (
            "none",
            Err(legacy.config_error.clone().unwrap_or_else(|| {
                "no notification settings; notifications are logged only (dry run)".to_owned()
            })),
        ),
    }
}

fn set_notifications(config: &mut Value, section: Value) -> std::io::Result<()> {
    match config.as_object_mut() {
        Some(map) => {
            map.insert("notifications".to_owned(), section);
            Ok(())
        }
        None => Err(std::io::Error::other(
            "config.json is not a JSON object; not overwriting it",
        )),
    }
}

/// Writes `settings` as the `notifications` section of the committed
/// config (durable first, then the tmpfs mirror) and of any staging copy,
/// so a later commit of unrelated staged edits cannot bring back the old
/// settings. When nothing was staged, nothing is staged afterwards (the
/// staging copy is written byte-identical to the committed config). Every
/// other field is kept as is. Callers hold `SAVE_LOCK`.
async fn write_notifications(
    paths: &ConfigPaths,
    settings: &NotificationSettings,
) -> std::io::Result<()> {
    let section = serde_json::to_value(settings).map_err(std::io::Error::other)?;
    let committed_text = durable_state::read_cached(&paths.config_cache_path)
        .await
        .ok();
    let preview_text = tokio::fs::read_to_string(&paths.preview_config_path)
        .await
        .ok();
    let was_staged = match (&preview_text, &committed_text) {
        (Some(preview), Some(committed)) => preview != committed,
        (Some(_), None) => true,
        _ => false,
    };
    let mut committed = match &committed_text {
        Some(text) => serde_json::from_str::<Value>(text).map_err(|error| {
            std::io::Error::other(format!(
                "config.json is not valid JSON ({error}); not overwriting it"
            ))
        })?,
        None => Value::Object(serde_json::Map::new()),
    };
    set_notifications(&mut committed, section.clone())?;
    let committed_new = serde_json::to_string_pretty(&committed).map_err(std::io::Error::other)?;
    durable_state::write_through(&paths.config_path, &paths.config_cache_path, &committed_new)
        .await?;
    let Some(preview) = preview_text else {
        return Ok(());
    };
    let preview_new = if was_staged {
        // A malformed staging copy is left alone; committing it would fail
        // on its own anyway.
        let Ok(mut staged) = serde_json::from_str::<Value>(&preview) else {
            return Ok(());
        };
        if set_notifications(&mut staged, section).is_err() {
            return Ok(());
        }
        serde_json::to_string_pretty(&staged).map_err(std::io::Error::other)?
    } else {
        committed_new
    };
    let temp = paths.preview_config_path.with_extension("json.tmp");
    tokio::fs::write(&temp, preview_new).await?;
    tokio::fs::rename(temp, &paths.preview_config_path).await
}

/// One-time import of the legacy `alerts.json` into `config.json`.
async fn import_legacy(paths: &ConfigPaths, legacy: &AlertsSetup) {
    let Some(settings) = &legacy.settings else {
        return;
    };
    let _guard = SAVE_LOCK.lock().await;
    let committed = read_committed(&paths.config_cache_path).await;
    if committed.as_ref().and_then(notifications_of).is_some() {
        tracing::info!(
            path = %resolve_config_path().display(),
            "config.json already has notification settings; the legacy alerts config is not used and can be deleted"
        );
        return;
    }
    match write_notifications(paths, settings).await {
        Ok(()) => tracing::info!(
            path = %resolve_config_path().display(),
            "imported the legacy alerts config into config.json; it is no longer read and can be deleted"
        ),
        Err(error) => tracing::warn!(
            %error,
            "could not import the legacy alerts config into config.json; using it for this run only"
        ),
    }
}

// ---------------------------------------------------------------------------
// Notification delivery
// ---------------------------------------------------------------------------

#[derive(Debug, Clone)]
enum Notifier {
    /// Log only. Used when no channel is configured, and in local tests.
    DryRun,
    Ntfy(NtfySender),
}

fn transition_style(transition: Transition) -> (u8, &'static str) {
    match transition {
        Transition::Fired | Transition::Reminder => (4, "warning"),
        Transition::Resolved => (3, "white_check_mark"),
    }
}

impl Notifier {
    fn channel(&self) -> &'static str {
        match self {
            Self::DryRun => "dry_run",
            Self::Ntfy(_) => "ntfy",
        }
    }

    async fn publish(
        &self,
        title: &str,
        message: &str,
        priority: u8,
        tag: &str,
    ) -> Result<(), String> {
        match self {
            Self::DryRun => {
                tracing::warn!(
                    %title,
                    %message,
                    "notification (dry run; no notification channel configured)"
                );
                Ok(())
            }
            Self::Ntfy(sender) => {
                sender
                    .run(publish_curl_config(
                        &sender.config,
                        title,
                        message,
                        priority,
                        tag,
                    ))
                    .await?;
                tracing::info!(%title, "notification delivered via ntfy");
                Ok(())
            }
        }
    }

    async fn deliver(
        &self,
        notification: &Notification,
        station_name: Option<&str>,
    ) -> Result<(), String> {
        let (priority, tag) = transition_style(notification.transition);
        self.publish(
            &notification.title(station_name),
            &notification.message(),
            priority,
            tag,
        )
        .await
    }
}

#[derive(Debug, Clone)]
struct NtfySender {
    config: NtfyConfig,
    /// The `curl` binary; overridable only by tests.
    curl: PathBuf,
}

impl NtfySender {
    /// Runs curl with `config` (a curl config file) on stdin.
    async fn run(&self, config: String) -> Result<(), String> {
        run_curl(&self.curl, config).await
    }
}

async fn run_curl(curl: &Path, config: String) -> Result<(), String> {
    // `-q` ignores any ~/.curlrc; `--config -` reads URL, headers, and
    // body from stdin so the token never appears in argv.
    let mut child = Command::new(curl)
        .args([
            "-q",
            "--silent",
            "--show-error",
            "--fail",
            "--proto",
            "=https,http",
            "--max-time",
            &CURL_TIMEOUT_SECS.to_string(),
            "--config",
            "-",
        ])
        .stdin(Stdio::piped())
        .stdout(Stdio::null())
        .stderr(Stdio::piped())
        .kill_on_drop(true)
        .spawn()
        .map_err(|error| format!("failed to start curl: {error}"))?;
    if let Some(mut stdin) = child.stdin.take() {
        stdin
            .write_all(config.as_bytes())
            .await
            .map_err(|error| format!("failed to write curl config: {error}"))?;
    }
    let output = tokio::time::timeout(
        std::time::Duration::from_secs(CURL_TIMEOUT_SECS + 5),
        child.wait_with_output(),
    )
    .await
    .map_err(|_| "curl did not exit in time".to_owned())?
    .map_err(|error| format!("curl failed: {error}"))?;
    if output.status.success() {
        return Ok(());
    }
    let stderr = String::from_utf8_lossy(&output.stderr);
    let stderr: String = stderr.trim().chars().take(200).collect();
    Err(format!("curl exited with {}: {stderr}", output.status))
}

/// Builds the curl config file (fed on stdin) for one ntfy JSON publish.
fn publish_curl_config(
    ntfy: &NtfyConfig,
    title: &str,
    message: &str,
    priority: u8,
    tag: &str,
) -> String {
    let body = serde_json::json!({
        "topic": ntfy.topic,
        "title": title,
        "message": message,
        "priority": priority,
        "tags": [tag],
    })
    .to_string();
    let mut config = format!("url = \"{}/\"\n", curl_escape(&ntfy.server));
    config.push_str("header = \"Content-Type: application/json\"\n");
    if let Some(token) = &ntfy.token {
        config.push_str(&format!(
            "header = \"Authorization: Bearer {}\"\n",
            curl_escape(token)
        ));
    }
    // `data-raw`, not `data`: never interpret a leading '@' as a file name.
    config.push_str(&format!("data-raw = \"{}\"\n", curl_escape(&body)));
    config
}

/// Escapes a value for a double-quoted curl config string.
pub(crate) fn curl_escape(value: &str) -> String {
    let mut escaped = String::with_capacity(value.len());
    for c in value.chars() {
        match c {
            '\\' => escaped.push_str("\\\\"),
            '"' => escaped.push_str("\\\""),
            '\n' => escaped.push_str("\\n"),
            '\r' => escaped.push_str("\\r"),
            '\t' => escaped.push_str("\\t"),
            _ => escaped.push(c),
        }
    }
    escaped
}

// ---------------------------------------------------------------------------
// Status snapshot (served read-only at GET /api/alerts)
// ---------------------------------------------------------------------------

#[derive(Debug, Clone, Serialize)]
pub struct ConditionStatus {
    pub condition: Condition,
    /// `clear`, `pending`, `firing`, or `recovering`.
    pub state: &'static str,
    pub since: Option<DateTime<Utc>>,
    pub last_notified_at: Option<DateTime<Utc>>,
    pub detail: Option<String>,
}

#[derive(Debug, Clone, Default, Serialize)]
pub struct DigestStatus {
    pub enabled: bool,
    pub send_at: Option<String>,
    pub timezone: String,
    pub next_due_at: Option<DateTime<Utc>>,
    /// End of the last window sent (or skipped).
    pub last_window_end: Option<DateTime<Utc>>,
    pub last_sent_at: Option<DateTime<Utc>>,
    /// A digest is waiting for delivery.
    pub pending: bool,
    pub last_error: Option<String>,
}

#[derive(Debug, Clone, Serialize)]
pub struct HeartbeatStatus {
    /// `disabled`, `dry_run`, `ok`, `withheld`, or `failing`.
    pub state: &'static str,
    pub interval_secs: Option<u64>,
    pub alert_after_secs: Option<u64>,
    pub last_checkin_at: Option<DateTime<Utc>>,
    pub next_checkin_at: Option<DateTime<Utc>>,
    pub withheld_reason: Option<String>,
    pub last_error: Option<String>,
}

impl Default for HeartbeatStatus {
    fn default() -> Self {
        Self {
            state: "disabled",
            interval_secs: None,
            alert_after_secs: None,
            last_checkin_at: None,
            next_checkin_at: None,
            withheld_reason: None,
            last_error: None,
        }
    }
}

/// Never contains the ntfy topic, token, sequence ID, or config path.
#[derive(Debug, Clone, Serialize)]
pub struct AlertsStatus {
    pub channel: &'static str,
    /// Where the settings came from: `config`, `alerts_file`, or `none`.
    pub settings_source: &'static str,
    pub config_error: Option<String>,
    pub config_warnings: Vec<String>,
    pub poll_interval_secs: u64,
    pub last_evaluated_at: Option<DateTime<Utc>>,
    /// Conditions currently Firing or Recovering (notified, not resolved).
    pub active_count: usize,
    pub conditions: Vec<ConditionStatus>,
    pub outbox_len: usize,
    pub last_delivered_at: Option<DateTime<Utc>>,
    pub last_delivery_error: Option<String>,
    pub thresholds: Thresholds,
    pub digest: DigestStatus,
    pub heartbeat: HeartbeatStatus,
}

impl Monitor {
    fn condition_statuses(&self) -> Vec<ConditionStatus> {
        Condition::ALL
            .iter()
            .map(|&condition| {
                let tracker = &self.trackers[condition.index()];
                let (state, since, last_notified_at) = match tracker.debouncer.phase {
                    Phase::Clear => ("clear", None, None),
                    Phase::Pending { since } => ("pending", Some(since), None),
                    Phase::Firing {
                        since,
                        last_notified,
                    } => ("firing", Some(since), Some(last_notified)),
                    Phase::Recovering {
                        since,
                        last_notified,
                        ..
                    } => ("recovering", Some(since), Some(last_notified)),
                };
                ConditionStatus {
                    condition,
                    state,
                    since,
                    last_notified_at,
                    detail: tracker.detail.clone(),
                }
            })
            .collect()
    }

    /// Titles of conditions that are notified and not yet resolved; with
    /// `capture_path_only`, just the ones that withhold the heartbeat
    /// (`docs/optic-daemon-digest-heartbeat.md` §4.3).
    fn active_titles(&self, capture_path_only: bool) -> Vec<&'static str> {
        self.condition_statuses()
            .into_iter()
            .filter(|status| matches!(status.state, "firing" | "recovering"))
            .filter(|status| {
                !capture_path_only
                    || matches!(
                        status.condition,
                        Condition::CaptureStalled
                            | Condition::CaptureOverdue
                            | Condition::CaptureFailing
                    )
            })
            .map(|status| status.condition.title())
            .collect()
    }
}

// ---------------------------------------------------------------------------
// Actor
// ---------------------------------------------------------------------------

/// The existing handles the monitor reads from. All reads are
/// non-mutating, except that the actor writes `config.json`'s
/// `notifications` section once to import the legacy file, and its own
/// digest state file.
pub struct AlertSources {
    pub scheduler: SchedulerHandle,
    pub sync: DataSyncManager,
    pub capture_log: Option<CaptureLog>,
    pub system_status: SystemStatusReader,
    pub config_paths: ConfigPaths,
    pub events: Option<SystemEventLog>,
    /// `digest_state.json` in the state directory.
    pub digest_state_path: PathBuf,
    /// Whether `OpticCamera::probe` found the camera at startup.
    pub camera_detected: bool,
    pub version: &'static str,
}

/// Why a test or on-demand digest was not sent.
#[derive(Debug, Clone, PartialEq)]
pub enum SendError {
    /// No usable channel (dry run); carries the reason.
    NotConfigured(String),
    /// At most one test/on-demand send per `MANUAL_SEND_SPACING`.
    RateLimited,
    Failed(String),
}

const MANUAL_SEND_SPACING: Duration = Duration::seconds(10);

enum ActorCommand {
    /// Re-read the settings and evaluate now (sent after a save).
    Reload,
    Test {
        reply: oneshot::Sender<Result<(), SendError>>,
    },
    DigestNow {
        reply: oneshot::Sender<Result<(), SendError>>,
    },
}

#[derive(Clone)]
pub struct AlertsHandle {
    status: watch::Receiver<AlertsStatus>,
    commands: mpsc::Sender<ActorCommand>,
    legacy: Arc<AlertsSetup>,
    paths: ConfigPaths,
}

impl AlertsHandle {
    pub fn spawn(legacy: AlertsSetup, sources: AlertSources) -> Self {
        let monitor = Monitor::new(legacy.thresholds.clone(), Utc::now());
        let (status_tx, status) = watch::channel(AlertsStatus {
            channel: Notifier::DryRun.channel(),
            settings_source: "none",
            config_error: Some("not evaluated yet".to_owned()),
            config_warnings: Vec::new(),
            poll_interval_secs: POLL_INTERVAL.as_secs(),
            last_evaluated_at: None,
            active_count: 0,
            conditions: monitor.condition_statuses(),
            outbox_len: 0,
            last_delivered_at: None,
            last_delivery_error: None,
            thresholds: legacy.thresholds.clone(),
            digest: DigestStatus::default(),
            heartbeat: HeartbeatStatus::default(),
        });
        let (commands, receiver) = mpsc::channel(8);
        let handle = Self {
            status,
            commands,
            legacy: Arc::new(legacy.clone()),
            paths: sources.config_paths.clone(),
        };
        tokio::spawn(run_actor(legacy, sources, monitor, status_tx, receiver));
        handle
    }

    pub fn status(&self) -> AlertsStatus {
        self.status.borrow().clone()
    }

    pub async fn reload(&self) {
        let _ = self.commands.send(ActorCommand::Reload).await;
    }

    async fn request(
        &self,
        make: impl FnOnce(oneshot::Sender<Result<(), SendError>>) -> ActorCommand,
    ) -> Result<(), SendError> {
        let (reply, answer) = oneshot::channel();
        let not_running = || SendError::Failed("the alerts monitor is not running".to_owned());
        self.commands
            .send(make(reply))
            .await
            .map_err(|_| not_running())?;
        answer.await.map_err(|_| not_running())?
    }

    /// Sends a test notification through the saved channel.
    pub async fn send_test(&self) -> Result<(), SendError> {
        self.request(|reply| ActorCommand::Test { reply }).await
    }

    /// Sends a digest of the last 24 h now (does not affect the daily one).
    pub async fn send_digest_now(&self) -> Result<(), SendError> {
        self.request(|reply| ActorCommand::DigestNow { reply })
            .await
    }

    /// The settings as the Config page sees them (no secrets).
    pub async fn settings_view(&self) -> NotificationsView {
        let config = read_committed(&self.paths.config_cache_path).await;
        let (source, settings) = effective_settings(config.as_ref(), &self.legacy);
        NotificationsView::new(source, settings.as_ref().map_err(String::as_str))
    }

    /// Validates and saves a Config page update into `config.json`, then
    /// applies it without a restart.
    pub async fn save_settings(
        &self,
        update: NotificationsUpdate,
    ) -> Result<NotificationsView, SaveError> {
        let merged = {
            let _guard = SAVE_LOCK.lock().await;
            let config = read_committed(&self.paths.config_cache_path).await;
            let (_, current) = effective_settings(config.as_ref(), &self.legacy);
            let merged = merge_update(current.ok().as_ref(), update);
            validate_for_save(&merged).map_err(SaveError::Invalid)?;
            write_notifications(&self.paths, &merged)
                .await
                .map_err(|error| SaveError::Io(error.to_string()))?;
            merged
        };
        tracing::info!("notification settings saved from the dashboard");
        self.reload().await;
        Ok(NotificationsView::new("config", Ok(&merged)))
    }
}

#[derive(Debug, Default)]
struct DeliveryState {
    last_delivered_at: Option<DateTime<Utc>>,
    last_error: Option<String>,
}

/// Delivers queued notifications in order, stopping at the first failure so
/// an outage costs one delivery attempt per tick.
async fn flush(
    outbox: &mut Outbox,
    notifier: &Notifier,
    station_name: Option<&str>,
    delivery: &mut DeliveryState,
) {
    while let Some(notification) = outbox.queue.front() {
        match notifier.deliver(notification, station_name).await {
            Ok(()) => {
                outbox.queue.pop_front();
                delivery.last_delivered_at = Some(Utc::now());
                delivery.last_error = None;
            }
            Err(error) => {
                tracing::warn!(%error, queued = outbox.queue.len(), "health alert delivery failed; will retry");
                delivery.last_error = Some(error);
                return;
            }
        }
    }
}

/// Signals gathered alongside the `Observation`, used by the digest.
#[derive(Debug, Clone)]
struct Extras {
    sync: SyncStatus,
    state_disk: Option<(u64, u64)>,
    uptime_secs: u64,
}

#[derive(Debug, Default)]
struct HeartbeatRuntime {
    /// Where the pending scheduled message lives, as far as this process
    /// knows.
    armed_on: Option<ArmedOn>,
    /// A message orphaned by a settings change, to cancel before
    /// `deadline` (when it would be delivered anyway).
    pending_cancel: Option<(ArmedOn, DateTime<Utc>)>,
    withheld_reason: Option<String>,
    last_error: Option<String>,
    dry_run_logged_at: Option<DateTime<Utc>>,
}

#[derive(Debug, Default)]
struct DigestRuntime {
    pending: Option<(DateTime<Utc>, Digest)>,
    last_sent_at: Option<DateTime<Utc>>,
    last_error: Option<String>,
}

struct Actor {
    sources: AlertSources,
    legacy: AlertsSetup,
    source: &'static str,
    /// The settings currently applied; `None` before the first tick.
    effective: Option<Result<NotificationSettings, String>>,
    setup: AlertsSetup,
    monitor: Monitor,
    tracker: OutcomeTracker,
    outbox: Outbox,
    delivery: DeliveryState,
    digest_state: DigestState,
    dirty: bool,
    started_at: DateTime<Utc>,
    heartbeat: HeartbeatRuntime,
    digest: DigestRuntime,
    last_manual_send_at: Option<DateTime<Utc>>,
    tz: Tz,
    last_observation: Option<(Observation, Extras)>,
    /// The `curl` binary used to cancel an orphaned heartbeat.
    curl: PathBuf,
}

fn station_tz(schedule: &ScheduleConfig) -> Tz {
    schedule
        .station
        .as_ref()
        .and_then(|station| station.timezone.parse().ok())
        .unwrap_or(chrono_tz::UTC)
}

fn local_time(at: DateTime<Utc>, tz: Tz) -> String {
    at.with_timezone(&tz).format("%a %H:%M %Z").to_string()
}

async fn run_actor(
    legacy: AlertsSetup,
    sources: AlertSources,
    monitor: Monitor,
    status_tx: watch::Sender<AlertsStatus>,
    mut commands: mpsc::Receiver<ActorCommand>,
) {
    import_legacy(&sources.config_paths, &legacy).await;
    let (digest_state, warning) = DigestState::load(&sources.digest_state_path);
    if let Some(warning) = warning {
        tracing::warn!(%warning, path = %sources.digest_state_path.display(), "digest state");
    }
    let mut actor = Actor {
        sources,
        legacy,
        source: "none",
        effective: None,
        setup: dry_run_setup("not evaluated yet"),
        monitor,
        tracker: OutcomeTracker::default(),
        outbox: Outbox::default(),
        delivery: DeliveryState::default(),
        digest_state,
        dirty: false,
        started_at: Utc::now(),
        heartbeat: HeartbeatRuntime::default(),
        digest: DigestRuntime::default(),
        last_manual_send_at: None,
        tz: chrono_tz::UTC,
        last_observation: None,
        curl: PathBuf::from("curl"),
    };
    let mut interval = tokio::time::interval(POLL_INTERVAL);
    interval.set_missed_tick_behavior(tokio::time::MissedTickBehavior::Delay);
    let mut commands_open = true;
    loop {
        tokio::select! {
            _ = interval.tick() => actor.tick().await,
            command = commands.recv(), if commands_open => match command {
                Some(ActorCommand::Reload) => actor.tick().await,
                Some(ActorCommand::Test { reply }) => {
                    let _ = reply.send(actor.send_test().await);
                }
                Some(ActorCommand::DigestNow { reply }) => {
                    let _ = reply.send(actor.send_digest_now().await);
                }
                None => commands_open = false,
            },
        }
        status_tx.send_modify(|status| actor.fill_status(status));
    }
}

impl Actor {
    async fn tick(&mut self) {
        let now = Utc::now();
        let config = read_committed(&self.sources.config_paths.config_cache_path).await;
        let schedule = config
            .as_ref()
            .and_then(|config| config.get("schedule"))
            .and_then(|schedule| serde_json::from_value::<ScheduleConfig>(schedule.clone()).ok())
            .unwrap_or_default();
        self.tz = station_tz(&schedule);
        self.apply_settings(now, config.as_ref());

        let (observation, extras) = gather(
            &self.sources,
            &mut self.tracker,
            &self.monitor.thresholds,
            schedule,
            now,
        )
        .await;
        for notification in self.monitor.observe(&observation) {
            tracing::info!(
                condition = ?notification.condition,
                transition = ?notification.transition,
                detail = %notification.detail,
                "health alert state change"
            );
            if notification.transition == Transition::Fired {
                self.digest_state
                    .record_alert(now, notification.condition.title());
                self.dirty = true;
            }
            self.outbox.push(notification);
        }
        flush(
            &mut self.outbox,
            &self.setup.notifier,
            self.setup.station_name.as_deref(),
            &mut self.delivery,
        )
        .await;

        self.dirty |= self
            .digest_state
            .record_run_state(now, observation.scheduler_running);
        self.dirty |= self.digest_state.record_sample(
            now,
            Sample {
                cpu_temp_celsius: observation.cpu_temp_celsius,
                capture_disk: observation.capture_disk,
                transferred: Some((extras.sync.transferred_files, extras.sync.transferred_bytes)),
            },
        );
        self.digest_state.prune(now);

        self.heartbeat_step(now).await;
        self.digest_step(now, &observation, &extras).await;
        self.last_observation = Some((observation, extras));
        self.persist().await;
    }

    /// Applies the settings in effect if they changed since the last tick.
    fn apply_settings(&mut self, now: DateTime<Utc>, config: Option<&Value>) {
        let (source, effective) = effective_settings(config, &self.legacy);
        if self.source == source && self.effective.as_ref() == Some(&effective) {
            return;
        }
        let setup = match (&effective, source) {
            // Keeps the legacy file's own warnings (e.g. file mode).
            (Ok(_), "alerts_file") => self.legacy.clone(),
            (Ok(settings), _) => resolve(settings),
            (Err(reason), _) => dry_run_setup(reason),
        };
        let new_armed = match (&setup.heartbeat, &setup.notifier) {
            (Some(plan), Notifier::Ntfy(sender)) => {
                Some(ArmedOn::new(&sender.config, &plan.sequence_id))
            }
            _ => None,
        };
        let last_checkin = self.digest_state.heartbeat_last_checkin;
        if self.effective.is_none() {
            // First tick after a start: a message armed by the previous run
            // is assumed to be on the current channel.
            if let Some(plan) = &setup.heartbeat
                && optic_heartbeat::is_armed(last_checkin, now, plan.alert_after)
            {
                self.heartbeat.armed_on = new_armed.clone();
            }
        } else if optic_heartbeat::cancel_needed(
            self.heartbeat.armed_on.as_ref(),
            new_armed.as_ref(),
        ) && let Some(armed) = self.heartbeat.armed_on.take()
        {
            let old_alert_after = self.setup.heartbeat.as_ref().map_or(
                Duration::seconds(optic_heartbeat::MAX_ALERT_AFTER_SECS as i64),
                |plan| plan.alert_after,
            );
            if let Some(last) = last_checkin
                && optic_heartbeat::is_armed(Some(last), now, old_alert_after)
            {
                tracing::info!(
                    "notification settings changed; cancelling the armed heartbeat on the previous channel"
                );
                self.heartbeat.pending_cancel = Some((armed, last + old_alert_after));
            }
            // The new channel starts fresh: check in at once, and no false
            // "checking in again" notice.
            self.digest_state.heartbeat_last_checkin = None;
            self.dirty = true;
        }
        match &setup.config_error {
            Some(error) => tracing::warn!(source, %error, "notifications running in dry-run mode"),
            None => tracing::info!(
                source,
                channel = setup.notifier.channel(),
                digest = setup.digest_send_at.is_some(),
                heartbeat = setup.heartbeat.is_some(),
                "notification settings applied"
            ),
        }
        for warning in &setup.config_warnings {
            tracing::warn!(%warning, "notification settings warning");
        }
        self.monitor.thresholds = setup.thresholds.clone();
        self.setup = setup;
        self.source = source;
        self.effective = Some(effective);
    }

    fn heartbeat_state(&self) -> &'static str {
        match (&self.setup.heartbeat, &self.setup.notifier) {
            (None, _) => "disabled",
            (Some(_), Notifier::DryRun) => "dry_run",
            _ if self.heartbeat.withheld_reason.is_some() => "withheld",
            _ if self.heartbeat.last_error.is_some() => "failing",
            _ => "ok",
        }
    }

    async fn heartbeat_step(&mut self, now: DateTime<Utc>) {
        if let Some((armed, deadline)) = self.heartbeat.pending_cancel.clone() {
            if now >= deadline {
                tracing::warn!(
                    "the heartbeat on the previous channel could not be cancelled before it was delivered"
                );
                self.heartbeat.pending_cancel = None;
            } else {
                match run_curl(&self.curl, optic_heartbeat::cancel_curl_config(&armed)).await {
                    Ok(()) => {
                        tracing::info!("cancelled the heartbeat armed on the previous channel");
                        self.heartbeat.pending_cancel = None;
                    }
                    // Already delivered or never stored: nothing to cancel.
                    Err(error) if error.contains("404") => {
                        self.heartbeat.pending_cancel = None;
                    }
                    Err(error) => {
                        tracing::warn!(%error, "cancelling the previous heartbeat failed; will retry");
                        self.heartbeat.last_error = Some(format!("cancel failed: {error}"));
                    }
                }
            }
        }

        let Some(plan) = self.setup.heartbeat.clone() else {
            self.heartbeat.withheld_reason = None;
            return;
        };
        let withheld_by = self.monitor.active_titles(true);
        match optic_heartbeat::gate(&withheld_by, self.sources.camera_detected) {
            Err(reason) => {
                if self.heartbeat.withheld_reason.is_none() {
                    tracing::warn!(%reason, "heartbeat withheld");
                    self.digest_state.record_withheld(now);
                    self.dirty = true;
                }
                self.heartbeat.withheld_reason = Some(reason);
                return;
            }
            Ok(()) => {
                if self.heartbeat.withheld_reason.take().is_some() {
                    tracing::info!("heartbeat resumed");
                }
            }
        }
        let last = self.digest_state.heartbeat_last_checkin;
        let station = self.setup.station_name.clone();
        let sender = match &self.setup.notifier {
            Notifier::DryRun => {
                if self
                    .heartbeat
                    .dry_run_logged_at
                    .is_none_or(|at| now - at >= plan.interval)
                {
                    tracing::info!("heartbeat (dry run): would check in");
                    self.heartbeat.dry_run_logged_at = Some(now);
                }
                return;
            }
            Notifier::Ntfy(sender) => sender.clone(),
        };
        if !optic_heartbeat::is_due(last, now, &plan) {
            return;
        }
        let now_local = local_time(now, self.tz);
        let (title, message) =
            optic_heartbeat::silent_alert(station.as_deref(), plan.alert_after, &now_local);
        match sender
            .run(optic_heartbeat::arm_curl_config(
                &sender.config,
                &plan,
                &title,
                &message,
            ))
            .await
        {
            Ok(()) => {
                tracing::debug!("heartbeat checked in");
                self.digest_state.heartbeat_last_checkin = Some(now);
                self.dirty = true;
                self.heartbeat.last_error = None;
                self.heartbeat.armed_on = Some(ArmedOn::new(&sender.config, &plan.sequence_id));
                if let (Some(previous), Some(gap)) = (
                    last,
                    optic_heartbeat::silent_period(last, now, plan.alert_after),
                ) {
                    let (title, message) = optic_heartbeat::back_notice(
                        station.as_deref(),
                        &local_time(previous, self.tz),
                        &now_local,
                        &optic_digest::format_duration(gap),
                    );
                    if let Err(error) = self
                        .setup
                        .notifier
                        .publish(&title, &message, 3, "white_check_mark")
                        .await
                    {
                        tracing::warn!(%error, "could not send the heartbeat recovery notice");
                    }
                }
            }
            Err(error) => {
                tracing::warn!(%error, "heartbeat check-in failed; will retry next tick");
                self.heartbeat.last_error = Some(error);
            }
        }
    }

    async fn digest_step(
        &mut self,
        now: DateTime<Utc>,
        observation: &Observation,
        extras: &Extras,
    ) {
        if let Some(send_at) = self.setup.digest_send_at {
            match optic_digest::decide(now, self.tz, send_at, self.digest_state.last_digest_due) {
                Decision::Idle => {}
                Decision::Initialize { due } => {
                    self.digest_state.last_digest_due = Some(due);
                    self.dirty = true;
                }
                Decision::Skip { due } => {
                    tracing::warn!(%due, "daily digest skipped: more than 12 h late");
                    self.digest_state.last_digest_due = Some(due);
                    self.dirty = true;
                }
                Decision::Send { start, end } => {
                    let digest = self
                        .build_digest(start, end, now, observation, extras)
                        .await;
                    self.digest.pending = Some((end, digest));
                    self.digest_state.last_digest_due = Some(end);
                    self.dirty = true;
                }
            }
        }
        if let Some((due, digest)) = self.digest.pending.clone() {
            if now - due > optic_digest::CATCH_UP {
                tracing::warn!(%due, "daily digest dropped: undelivered for 12 h");
                self.digest.pending = None;
                return;
            }
            match self
                .setup
                .notifier
                .publish(&digest.title, &digest.message, 2, "bar_chart")
                .await
            {
                Ok(()) => {
                    tracing::info!(%due, "daily digest sent");
                    self.digest.pending = None;
                    self.digest.last_sent_at = Some(now);
                    self.digest.last_error = None;
                }
                Err(error) => {
                    tracing::warn!(%error, "daily digest delivery failed; will retry");
                    self.digest.last_error = Some(error);
                }
            }
        }
    }

    async fn build_digest(
        &self,
        start: DateTime<Utc>,
        end: DateTime<Utc>,
        now: DateTime<Utc>,
        observation: &Observation,
        extras: &Extras,
    ) -> Digest {
        let rows: Vec<CaptureRow> = match &self.sources.capture_log {
            Some(log) => log
                .window_rows(start.timestamp(), end.timestamp())
                .await
                .into_iter()
                .map(|row| CaptureRow {
                    at: Utc
                        .timestamp_opt(row.captured_at_unix, 0)
                        .single()
                        .unwrap_or(start),
                    scheduled: row.source == "scheduler",
                    success: row.success,
                    bytes: row.bytes_total,
                    error: row.error,
                })
                .collect(),
            None => Vec::new(),
        };
        let events: Vec<EventRow> = match &self.sources.events {
            Some(log) => log
                .list(200)
                .await
                .into_iter()
                .map(|event| EventRow {
                    at: Utc
                        .timestamp_millis_opt(event.occurred_at_unix_ms)
                        .single()
                        .unwrap_or(start),
                    unexpected: event
                        .detail
                        .pointer("/previous_boot/ended")
                        .and_then(Value::as_str)
                        == Some("unexpected"),
                    kind: event.kind,
                })
                .collect(),
            None => Vec::new(),
        };
        let heartbeat = self.setup.heartbeat.as_ref().map(|_| HeartbeatSnapshot {
            state: self.heartbeat_state().to_owned(),
            last_checkin: self.digest_state.heartbeat_last_checkin,
        });
        let sync = &extras.sync;
        optic_digest::build(&DigestInput {
            start,
            end,
            tz: self.tz,
            station_name: self.setup.station_name.as_deref(),
            schedule: &observation.schedule,
            rows: &rows,
            state: &self.digest_state,
            sync: Some(SyncSnapshot {
                enabled: sync.enabled,
                paused: sync.paused,
                queued_files: sync.queued_files,
                queued_bytes: sync.queued_bytes,
                connectivity: serde_json::to_value(sync.connectivity)
                    .ok()
                    .and_then(|value| value.as_str().map(str::to_owned))
                    .unwrap_or_else(|| "unknown".to_owned()),
                last_error: sync.last_error.clone(),
            }),
            capture_disk: observation.capture_disk,
            state_disk: extras.state_disk,
            active_alerts: self
                .monitor
                .active_titles(false)
                .into_iter()
                .map(str::to_owned)
                .collect(),
            events: &events,
            heartbeat,
            host_uptime_secs: Some(extras.uptime_secs),
            daemon_started_at: self.started_at,
            version: self.sources.version,
            now,
        })
    }

    /// Re-reads the settings (a save may have just happened) and applies the
    /// manual-send rules shared by the test and on-demand digest.
    async fn manual_send_allowed(&mut self, now: DateTime<Utc>) -> Result<(), SendError> {
        let config = read_committed(&self.sources.config_paths.config_cache_path).await;
        self.apply_settings(now, config.as_ref());
        if matches!(self.setup.notifier, Notifier::DryRun) {
            return Err(SendError::NotConfigured(
                self.setup
                    .config_error
                    .clone()
                    .unwrap_or_else(|| "notifications are turned off".to_owned()),
            ));
        }
        if self
            .last_manual_send_at
            .is_some_and(|at| now - at < MANUAL_SEND_SPACING)
        {
            return Err(SendError::RateLimited);
        }
        self.last_manual_send_at = Some(now);
        Ok(())
    }

    async fn send_test(&mut self) -> Result<(), SendError> {
        let now = Utc::now();
        self.manual_send_allowed(now).await?;
        let station = self
            .setup
            .station_name
            .as_deref()
            .map(|name| format!(" {name}"))
            .unwrap_or_default();
        self.setup
            .notifier
            .publish(
                &format!("Optic{station}: test notification"),
                &format!(
                    "Sent from the Config page at {}. Notifications are working.",
                    local_time(now, self.tz)
                ),
                3,
                "test_tube",
            )
            .await
            .map_err(SendError::Failed)
    }

    async fn send_digest_now(&mut self) -> Result<(), SendError> {
        let now = Utc::now();
        self.manual_send_allowed(now).await?;
        let Some((observation, extras)) = self.last_observation.clone() else {
            return Err(SendError::Failed(
                "no data gathered yet; try again in a few seconds".to_owned(),
            ));
        };
        let digest = self
            .build_digest(now - Duration::hours(24), now, now, &observation, &extras)
            .await;
        self.setup
            .notifier
            .publish(&digest.title, &digest.message, 2, "bar_chart")
            .await
            .map_err(SendError::Failed)
    }

    async fn persist(&mut self) {
        if !self.dirty {
            return;
        }
        let state = self.digest_state.clone();
        let path = self.sources.digest_state_path.clone();
        match tokio::task::spawn_blocking(move || state.save(&path)).await {
            Ok(Ok(())) => self.dirty = false,
            Ok(Err(error)) => tracing::warn!(%error, "could not save the digest state; will retry"),
            Err(error) => tracing::warn!(%error, "digest state save task failed"),
        }
    }

    fn fill_status(&self, status: &mut AlertsStatus) {
        let now = Utc::now();
        status.channel = self.setup.notifier.channel();
        status.settings_source = self.source;
        status.config_error = self.setup.config_error.clone();
        status.config_warnings = self.setup.config_warnings.clone();
        status.last_evaluated_at = self.monitor.last_evaluated_at;
        status.conditions = self.monitor.condition_statuses();
        status.active_count = status
            .conditions
            .iter()
            .filter(|c| matches!(c.state, "firing" | "recovering"))
            .count();
        status.outbox_len = self.outbox.queue.len();
        status.last_delivered_at = self.delivery.last_delivered_at;
        status.last_delivery_error = self.delivery.last_error.clone();
        status.thresholds = self.setup.thresholds.clone();
        status.digest = DigestStatus {
            enabled: self.setup.digest_send_at.is_some(),
            send_at: self
                .setup
                .digest_send_at
                .map(|at| at.format("%H:%M").to_string()),
            timezone: self.tz.name().to_owned(),
            next_due_at: self.setup.digest_send_at.map(|send_at| {
                optic_digest::next_due(
                    optic_digest::due_at(now, self.tz, send_at),
                    self.tz,
                    send_at,
                )
            }),
            last_window_end: self.digest_state.last_digest_due,
            last_sent_at: self.digest.last_sent_at,
            pending: self.digest.pending.is_some(),
            last_error: self.digest.last_error.clone(),
        };
        let plan = self.setup.heartbeat.as_ref();
        let state = self.heartbeat_state();
        let last_checkin = self.digest_state.heartbeat_last_checkin;
        status.heartbeat = HeartbeatStatus {
            state,
            interval_secs: plan.map(|plan| plan.interval.num_seconds() as u64),
            alert_after_secs: plan.map(|plan| plan.alert_after.num_seconds() as u64),
            last_checkin_at: last_checkin,
            next_checkin_at: match (state, plan) {
                ("ok" | "failing", Some(plan)) => {
                    Some(last_checkin.map_or(now, |at| at + plan.interval))
                }
                _ => None,
            },
            withheld_reason: self.heartbeat.withheld_reason.clone(),
            last_error: self.heartbeat.last_error.clone(),
        };
    }
}

async fn gather(
    sources: &AlertSources,
    tracker: &mut OutcomeTracker,
    thresholds: &Thresholds,
    schedule: ScheduleConfig,
    now: DateTime<Utc>,
) -> (Observation, Extras) {
    let scheduler = sources.scheduler.status();
    tracker.record(scheduler.last_capture.as_ref());
    let (recent_outcomes, last_success_at) = match &sources.capture_log {
        Some(log) => {
            let limit = thresholds.capture_failures_in_a_row.clamp(1, 100);
            let recent = log
                .query(scheduled_filter(None, limit))
                .await
                .entries
                .into_iter()
                .map(|entry| Outcome {
                    at: unix_ms_to_utc(entry.completed_at_unix_ms),
                    success: entry.success,
                    error: entry.error,
                })
                .collect();
            let last_success = log
                .query(scheduled_filter(Some(true), 1))
                .await
                .entries
                .first()
                .map(|entry| unix_ms_to_utc(entry.completed_at_unix_ms));
            (recent, last_success)
        }
        None => (
            tracker.recent.iter().cloned().collect(),
            tracker.last_success_at,
        ),
    };
    let sync = sources.sync.status();
    let system = sources.system_status.snapshot().await;
    let disk = |label: &str| {
        system
            .disks
            .iter()
            .find(|disk| disk.label == label)
            .map(|disk| (disk.total_bytes, disk.available_bytes))
    };
    let observation = Observation {
        now,
        scheduler_running: scheduler.run_state == ScheduleRunState::Running,
        next_capture_at: scheduler.next_capture_at,
        schedule,
        recent_outcomes,
        last_success_at,
        sync: Some(SyncObservation {
            enabled: sync.enabled,
            paused: sync.paused,
            queued_files: sync.queued_files,
            queued_bytes: sync.queued_bytes,
            transferred_files: sync.transferred_files,
            last_error: sync.last_error.clone(),
        }),
        capture_disk: disk("capture"),
        cpu_temp_celsius: system.cpu_temp_celsius,
        throttled: read_throttled().await,
    };
    let extras = Extras {
        state_disk: disk("state"),
        uptime_secs: system.uptime_seconds,
        sync,
    };
    (observation, extras)
}

fn scheduled_filter(success: Option<bool>, limit: u32) -> CaptureQueryFilter {
    CaptureQueryFilter {
        source: Some("scheduler".to_owned()),
        success,
        limit,
        ..CaptureQueryFilter::default()
    }
}

fn unix_ms_to_utc(ms: u128) -> DateTime<Utc> {
    Utc.timestamp_millis_opt(i64::try_from(ms).unwrap_or(i64::MAX))
        .single()
        .unwrap_or(DateTime::<Utc>::MIN_UTC)
}

#[cfg(target_os = "linux")]
async fn read_throttled() -> Option<u32> {
    let output = Command::new("vcgencmd")
        .arg("get_throttled")
        .output()
        .await
        .ok()?;
    if !output.status.success() {
        return None;
    }
    parse_throttled(&String::from_utf8_lossy(&output.stdout))
}

#[cfg(not(target_os = "linux"))]
async fn read_throttled() -> Option<u32> {
    None
}
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
