keefo/optic/src/camera.rs

#![cfg_attr(not(target_os = "linux"), allow(dead_code))]

use std::fmt;

use bytes::Bytes;
use serde::{Deserialize, Serialize};

#[derive(Debug, Clone, Deserialize, Serialize)]
#[serde(default, deny_unknown_fields)]
pub struct CameraSettings {
    pub rotation: u16,
    pub horizontal_flip: bool,
    pub vertical_flip: bool,
    pub awb: String,
    pub metering: String,
    pub exposure: String,
    pub ev: f32,
    pub gain: f32,
    pub shutter_us: u64,
    pub denoise: String,
    /// Manual white balance as `[red, blue]` colour gains. `Some` disables
    /// AWB for the request (`AwbEnable(false)` + `ColourGains`); `None`
    /// keeps per-frame AWB with `awb`'s mode. Set by exposure ramping
    /// (`docs/optic-daemon-exposure-ramping.md` §6), never by the dashboard.
    pub colour_gains: Option<[f32; 2]>,
}

/// Manual shutter range accepted by `CameraSettings::validate` (0 = auto).
pub(crate) const MIN_SHUTTER_US: u64 = 100;
pub(crate) const MAX_SHUTTER_US: u64 = 5_000_000;
/// Manual analogue gain range (0 = auto).
pub(crate) const MIN_GAIN: f32 = 1.0;
pub(crate) const MAX_GAIN: f32 = 16.0;
/// Manual colour-gain range for `CameraSettings::colour_gains`.
pub(crate) const COLOUR_GAIN_MIN: f32 = 0.5;
pub(crate) const COLOUR_GAIN_MAX: f32 = 8.0;

impl Default for CameraSettings {
    fn default() -> Self {
        Self {
            rotation: 0,
            horizontal_flip: false,
            vertical_flip: false,
            // Daylight, not Auto: per-frame AWB makes consecutive timelapse
            // frames jump in colour, and a RAW/DNG keeps white balance
            // adjustable in post anyway (docs §6).
            awb: "daylight".to_owned(),
            metering: "centre".to_owned(),
            exposure: "normal".to_owned(),
            ev: 0.0,
            gain: 0.0,
            shutter_us: 0,
            denoise: "auto".to_owned(),
            colour_gains: None,
        }
    }
}

impl CameraSettings {
    pub(crate) fn validate(&self) -> Result<(), CameraError> {
        if !matches!(self.rotation, 0 | 180) {
            return Err(CameraError::Invalid("rotation must be 0 or 180"));
        }
        if !matches!(
            self.awb.as_str(),
            "auto" | "incandescent" | "tungsten" | "fluorescent" | "indoor" | "daylight" | "cloudy"
        ) {
            return Err(CameraError::Invalid("unsupported white-balance mode"));
        }
        if !matches!(self.metering.as_str(), "centre" | "spot" | "average") {
            return Err(CameraError::Invalid("unsupported metering mode"));
        }
        if !matches!(self.exposure.as_str(), "normal" | "sport") {
            return Err(CameraError::Invalid("unsupported exposure mode"));
        }
        if !matches!(
            self.denoise.as_str(),
            "auto" | "off" | "cdn_off" | "cdn_fast" | "cdn_hq"
        ) {
            return Err(CameraError::Invalid("unsupported denoise mode"));
        }
        if !(-4.0..=4.0).contains(&self.ev) || !self.ev.is_finite() {
            return Err(CameraError::Invalid("EV must be between -4 and 4"));
        }
        if !(self.gain == 0.0 || (MIN_GAIN..=MAX_GAIN).contains(&self.gain))
            || !self.gain.is_finite()
        {
            return Err(CameraError::Invalid(
                "gain must be 0 (auto) or between 1 and 16",
            ));
        }
        if !(self.shutter_us == 0 || (MIN_SHUTTER_US..=MAX_SHUTTER_US).contains(&self.shutter_us)) {
            return Err(CameraError::Invalid(
                "shutter must be 0 (auto) or between 100 and 5000000 microseconds",
            ));
        }
        if let Some(gains) = self.colour_gains
            && !gains
                .iter()
                .all(|gain| (COLOUR_GAIN_MIN..=COLOUR_GAIN_MAX).contains(gain))
        {
            return Err(CameraError::Invalid(
                "colour gains must be between 0.5 and 8",
            ));
        }
        Ok(())
    }
}

#[derive(Debug, Clone, Copy, Default, Deserialize, Eq, PartialEq, Serialize)]
#[serde(rename_all = "snake_case")]
pub enum CaptureProfile {
    #[default]
    MasterArchive,
    #[serde(rename = "dci_4k")]
    Dci4k,
    #[serde(rename = "binning_2k")]
    Binning2k,
}

#[derive(Debug, Clone, Deserialize, Serialize)]
#[serde(default)]
pub struct AppConfig {
    pub profile: CaptureProfile,
    pub settings: CameraSettings,
    /// The committed DNG preference for profiles that don't force one
    /// either way (`Dci4k`) — `MasterArchive`/`Binning2k` ignore this and
    /// always use their own forced value (`validate_raw_policy`). Mirrors
    /// `CaptureRequest::save_dng`'s shape, but for autonomous scheduled
    /// captures, which have no per-click UI checkbox to read from — see
    /// `docs/optic-daemon-scheduler.md` §6.
    pub save_dng: bool,
    /// Autonomous timelapse scheduling rules — see `optic_scheduler` and
    /// `docs/optic-daemon-scheduler.md`. `#[serde(default)]` at the
    /// container level (above) means a `config.json` committed before
    /// this field existed still deserializes fine, filling it with
    /// `ScheduleConfig::default()` (no rules, nothing scheduled).
    pub schedule: crate::optic_scheduler::ScheduleConfig,
    /// Notification settings (ntfy channel, digest, heartbeat, alert
    /// thresholds) — `docs/optic-daemon-digest-heartbeat.md` §5. Kept as
    /// raw JSON and parsed by `optic_alerts`, so a malformed section can
    /// never make the whole config fail to parse (which would silently
    /// fall back to defaults, schedule included). Holds the ntfy topic and
    /// token: `/api/status` masks it (`optic_alerts::redact_notifications`).
    #[serde(skip_serializing_if = "Option::is_none")]
    pub notifications: Option<serde_json::Value>,
}

impl Default for AppConfig {
    fn default() -> Self {
        Self {
            profile: CaptureProfile::Binning2k,
            settings: CameraSettings::default(),
            save_dng: false,
            schedule: crate::optic_scheduler::ScheduleConfig::default(),
            notifications: None,
        }
    }
}

impl CaptureProfile {
    pub(crate) fn spec(self) -> CaptureSpec {
        match self {
            Self::MasterArchive => CaptureSpec {
                slug: "master-archive",
                width: 4056,
                height: 3040,
                jpeg_quality: 100,
            },
            Self::Dci4k => CaptureSpec {
                slug: "4k-dci",
                width: 4056,
                height: 2160,
                jpeg_quality: 95,
            },
            Self::Binning2k => CaptureSpec {
                slug: "2k-binning",
                width: 2028,
                height: 1520,
                jpeg_quality: 85,
            },
        }
    }

    pub(crate) fn validate_raw_policy(self, save_dng: bool) -> Result<(), CameraError> {
        match (self, save_dng) {
            (Self::Binning2k, true) => Err(CameraError::Invalid(
                "2K Binning does not support companion DNG capture",
            )),
            _ => Ok(()),
        }
    }

    /// `downsample` only changes Master Archive, whose full-resolution
    /// preview is ~2.7 MB per frame; the other previews are already small.
    pub(crate) fn preview_spec(self, downsample: bool) -> PreviewSpec {
        match self {
            // Force the full-resolution mode and let the ISP scale down: left
            // to itself libcamera picks the IMX477's 1332x990 mode, a centre
            // crop that frames tighter than the capture, and the 2028x1520
            // binned mode looked visibly softer than full-size frames scaled
            // by the browser. Full mode still allows 8 fps (85 ms minimum).
            Self::MasterArchive if downsample => PreviewSpec {
                width: 1352,
                height: 1014,
                fps: 8,
                sensor_mode: Some((4056, 3040)),
            },
            Self::MasterArchive => PreviewSpec {
                width: 4056,
                height: 3040,
                fps: 2,
                sensor_mode: None,
            },
            Self::Dci4k => PreviewSpec {
                width: 1352,
                height: 720,
                fps: 8,
                sensor_mode: None,
            },
            Self::Binning2k => PreviewSpec {
                width: 1014,
                height: 760,
                fps: 8,
                sensor_mode: None,
            },
        }
    }

    pub(crate) fn raw_format(self) -> &'static str {
        match self {
            Self::MasterArchive | Self::Dci4k => "SBGGR12_CSI2P",
            Self::Binning2k => "SBGGR10_CSI2P",
        }
    }
}

#[derive(Debug, Clone, Copy)]
pub(crate) struct CaptureSpec {
    pub slug: &'static str,
    pub width: u32,
    pub height: u32,
    pub jpeg_quality: u8,
}

/// Shortest frame duration requested for still-capture warmup frames. libcamera
/// clamps it up to the selected sensor mode's minimum. Without an explicit
/// limit, still captures inherited the previous preview's limit (~500 ms per
/// frame after the 2 FPS Master Archive preview;
/// `docs/optic-daemon-capture-performance.md` §7).
pub(crate) const STILL_MIN_FRAME_DURATION_US: i64 = 33_333;

/// Longest frame duration allowed when the shutter is auto (`0`). Auto
/// exposure still runs in that case and is capped by the maximum frame
/// duration, so this must not undercut it; 500 ms matches the slowest
/// preview limit that still captures used to inherit.
pub(crate) const STILL_AUTO_MAX_FRAME_DURATION_US: i64 = 500_000;

/// Frames a still capture waits for before its output frame: the 3 queued
/// requests plus `native_camera.rs`'s 8 warmup frames. Each lasts at least
/// one shutter, which bounds how long a ramped shutter can be for a given
/// interval (`exposure_ramp::max_shutter_for_gap`).
pub(crate) const STILL_CAPTURE_FRAMES: u32 = 11;

/// How close a warmup frame's metadata exposure and gain must be to a manual
/// request for the frame to count as exposed as requested. The sensor
/// quantises: 3,440,629 µs requested ran at 3,474,267 µs (+1.0%).
const MANUAL_EXPOSURE_TOLERANCE: f64 = 0.05;
/// Largest frame-to-frame colour-gain change that counts as AWB settled.
const SETTLED_COLOUR_GAIN_TOLERANCE: f64 = 0.01;

/// One completed still-pipeline frame as the capture loop sees it: its
/// 1-based index and the metadata the camera reports for it.
#[derive(Debug, Clone, Copy, PartialEq)]
pub(crate) struct WarmupFrame {
    pub index: u32,
    pub exposure_us: Option<i32>,
    pub analogue_gain: Option<f32>,
    pub colour_gains: Option<[f32; 2]>,
}
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
