keefo/optic/src/web.rs

use std::{
    convert::Infallible,
    path::{Component, Path, PathBuf},
    sync::Arc,
    time::{Instant, SystemTime},
};

use axum::{
    Json, Router,
    body::Body,
    extract::{Path as PathParam, Query, State},
    http::{StatusCode, header},
    response::{IntoResponse, Response},
    routing::{get, post},
};
use bytes::{Bytes, BytesMut};
use serde::{Deserialize, Serialize};

use crate::{
    camera::{
        CameraError, CameraSettings, CaptureProfile, CaptureRequest, CaptureResult, PreviewFrame,
        StreamRequest,
    },
    durable_state,
    optic_alerts::{
        AlertsHandle, AlertsStatus, NotificationsUpdate, NotificationsView, SaveError, SendError,
    },
    optic_camera::{CameraBackendKind, OpticCamera},
    optic_capture_log::{CaptureHealthStatus, CaptureLog, CaptureLogEntry, CaptureQueryFilter},
    optic_events::{SystemEvent, SystemEventKind, SystemEventLog},
    optic_scheduler::{
        self, CelestialTarget, LunarEvent, MilkyWayEvent, SchedulerHandle, SchedulerStatus,
        SchedulerUnavailable, SolarEvent, Station,
    },
    optic_sync::{DataSyncManager, SyncStatus, SyncUnavailable},
    system_status::{self, SystemStatus, SystemStatusReader},
};

use crate::camera::AppConfig;

const SECURITY_POLICY: &str = "default-src 'self'; img-src 'self' blob: data:; script-src 'self'; style-src 'self'; object-src 'none'; base-uri 'none'; frame-ancestors 'none'";
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
